damouze/SZC-1/doc/memory_chip_pinouts.xlsx

AS6C4008-55PCN |  | SST39SF040 |  |  | AS6C4008-55PCN |  |  | SST39SF040
 |  |  |  |  | BUS | UNIT | BUS | UNIT | BUS
D3 | 17 | D3 | 17 | * | A14 | 3 | A14 | 29 | A14 | 1
D4 | 18 | D4 | 18 | * | A15 | 31 | A15 | 3 | A15 | 1
A15 | 31 | /WE | 31 | * | /WE | 29 | /WE | 31 | /WE | 1
