damouze/SZC-1/boards/core/power_board_v2/production/ATX_20-PIN.png

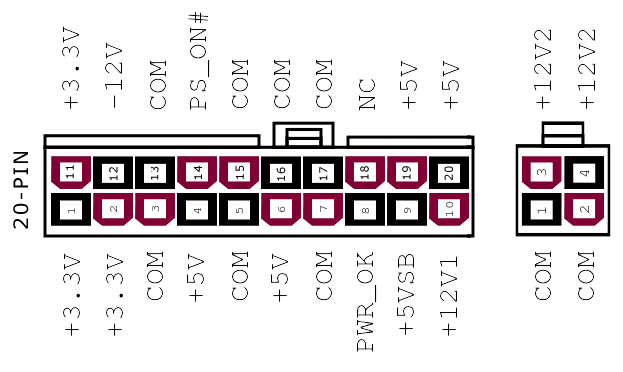
boards/core/power_board_v2/production/ATX_20-PIN.png
