damouze/SZC-1/boards/core/power_board_v2/production/J5.png

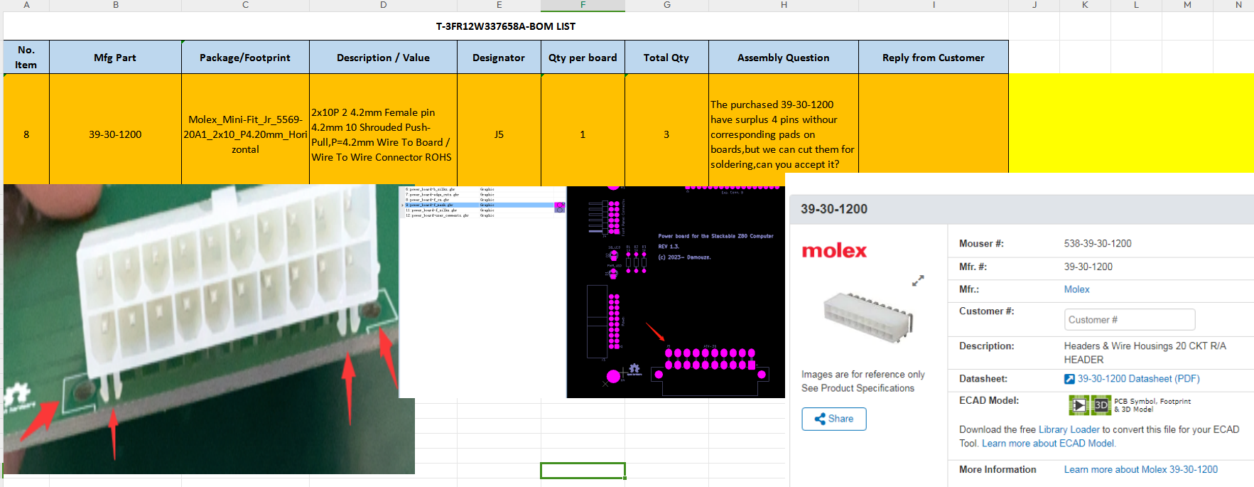
boards/core/power_board_v2/production/J5.png
