damouze/SZC-1/doc/Capture.PNG

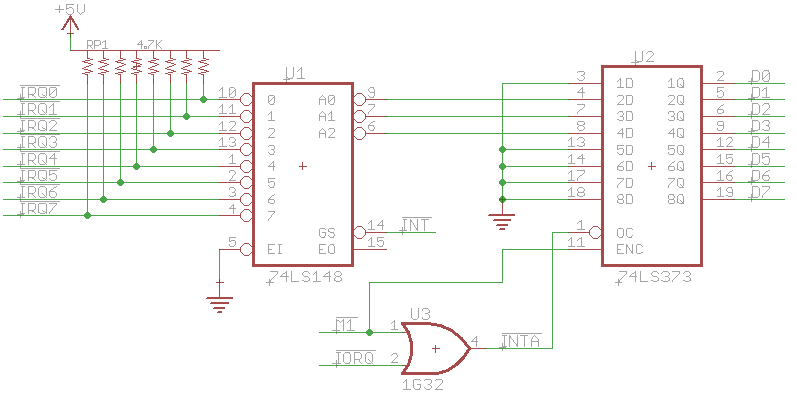
doc/Capture.PNG
