damouze/SZC-1/doc/Interrupt+Mode+2+Circuit.png

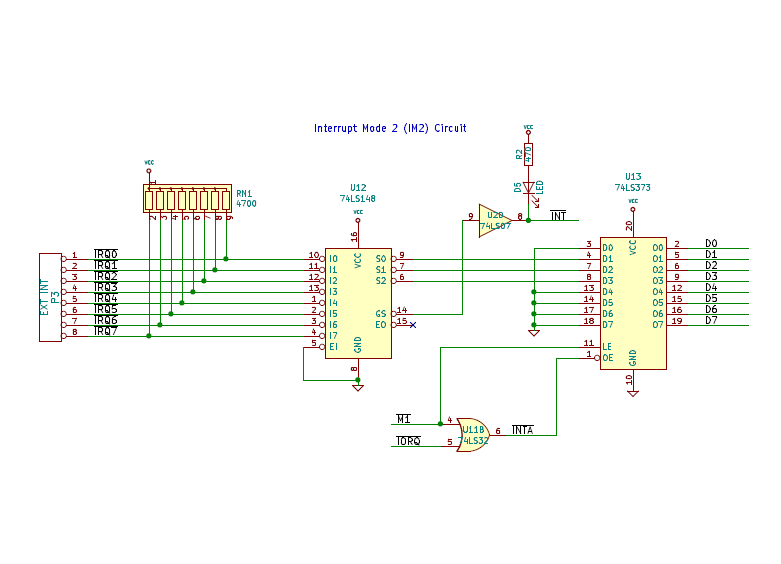
doc/Interrupt+Mode+2+Circuit.png
