damouze/SZC-1/pics/renderings/7seg_led_display_bottom.png

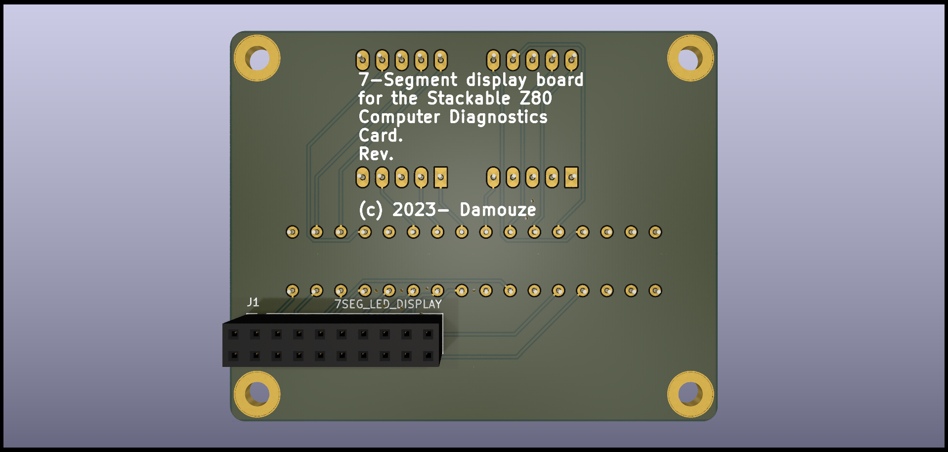
pics/renderings/7seg_led_display_bottom.png
