damouze/SZC-1/pics/renderings/7seg_led_display_top.png

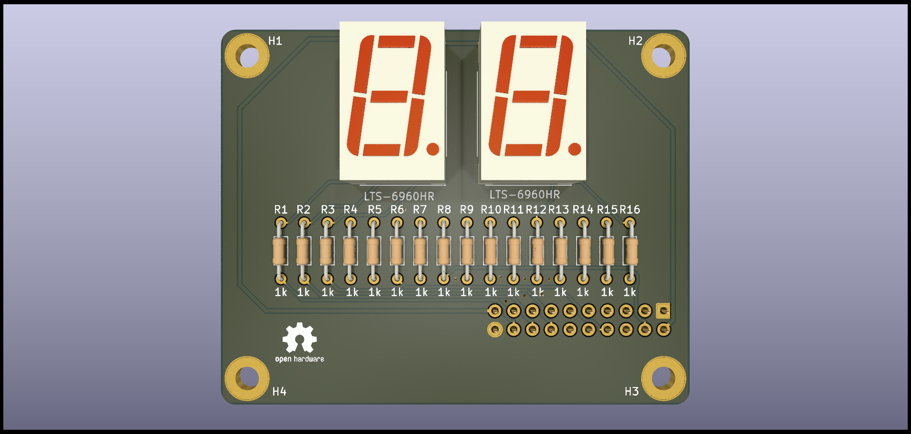
pics/renderings/7seg_led_display_top.png
