damouze/SZC-1/pics/renderings/audio_board_back.png

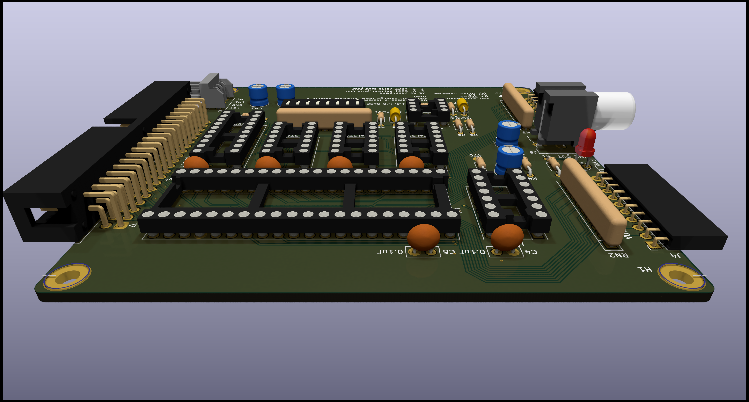
pics/renderings/audio_board_back.png
