damouze/SZC-1/pics/renderings/audio_board_bottom.png

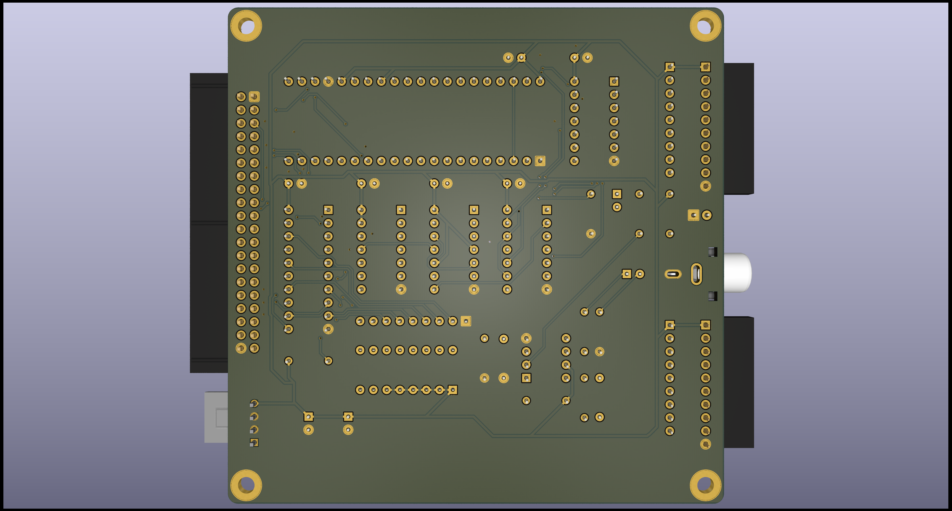
pics/renderings/audio_board_bottom.png
