damouze/SZC-1/pics/renderings/audio_board_front.png

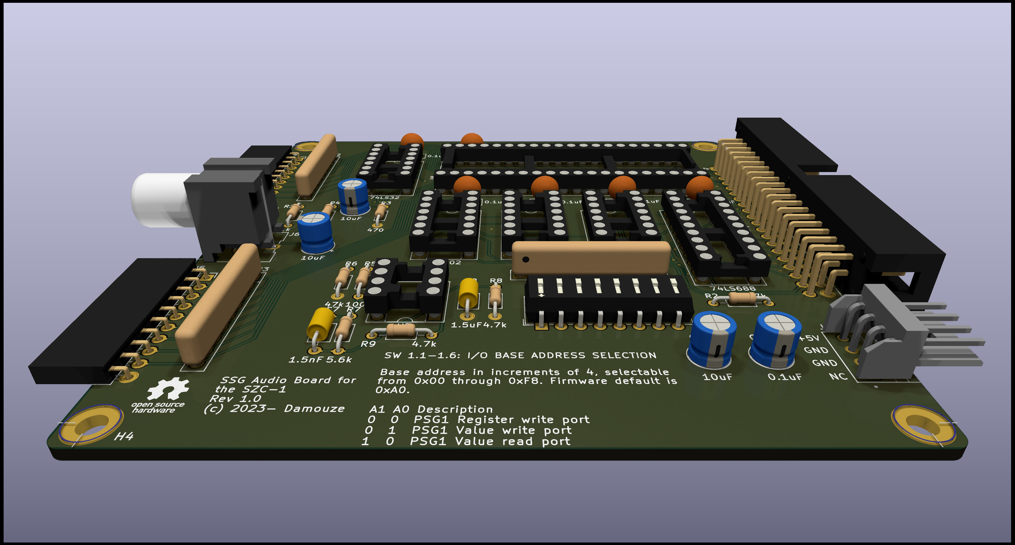
pics/renderings/audio_board_front.png
