damouze/SZC-1/pics/renderings/audio_board_left.png

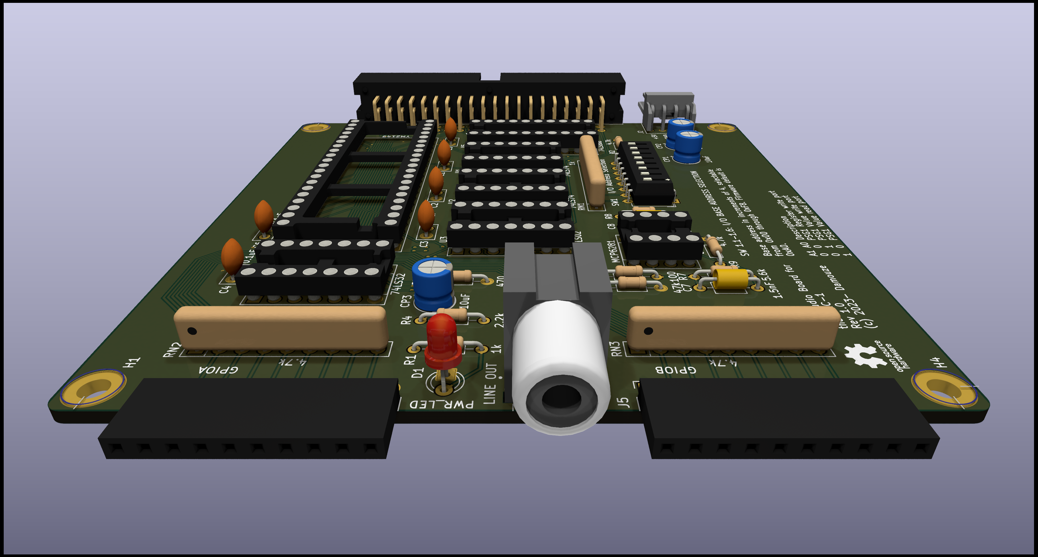
pics/renderings/audio_board_left.png
