damouze/SZC-1/pics/renderings/audio_board_left_unrouted.png

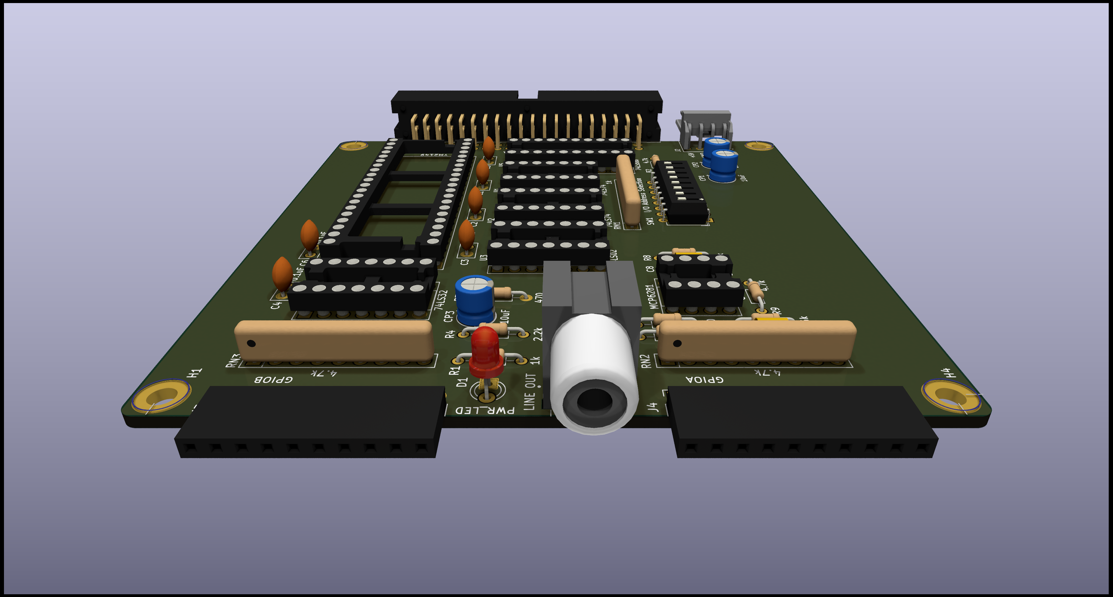
pics/renderings/audio_board_left_unrouted.png
