damouze/SZC-1/pics/renderings/audio_board_right.png

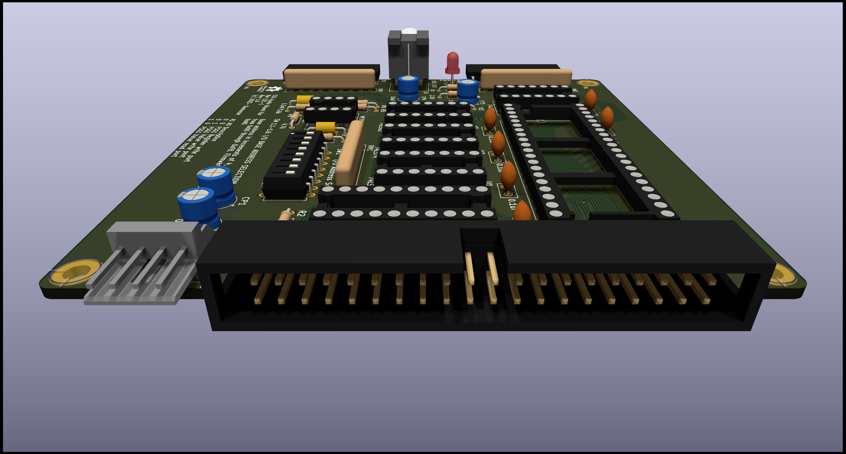
pics/renderings/audio_board_right.png
