damouze/SZC-1/pics/renderings/audio_board_top.png

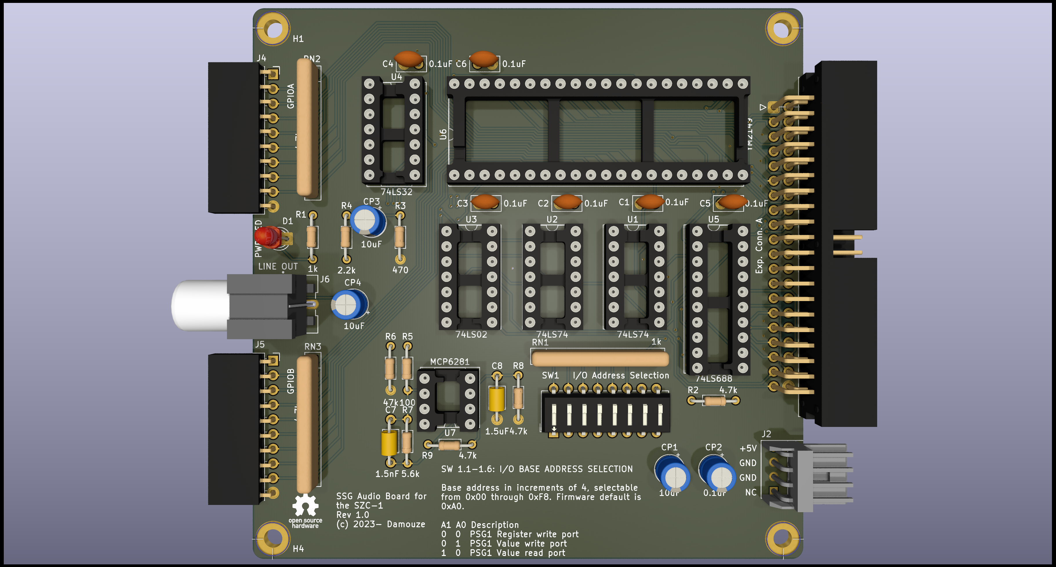
pics/renderings/audio_board_top.png
