damouze/SZC-1/pics/renderings/bus_decode.png

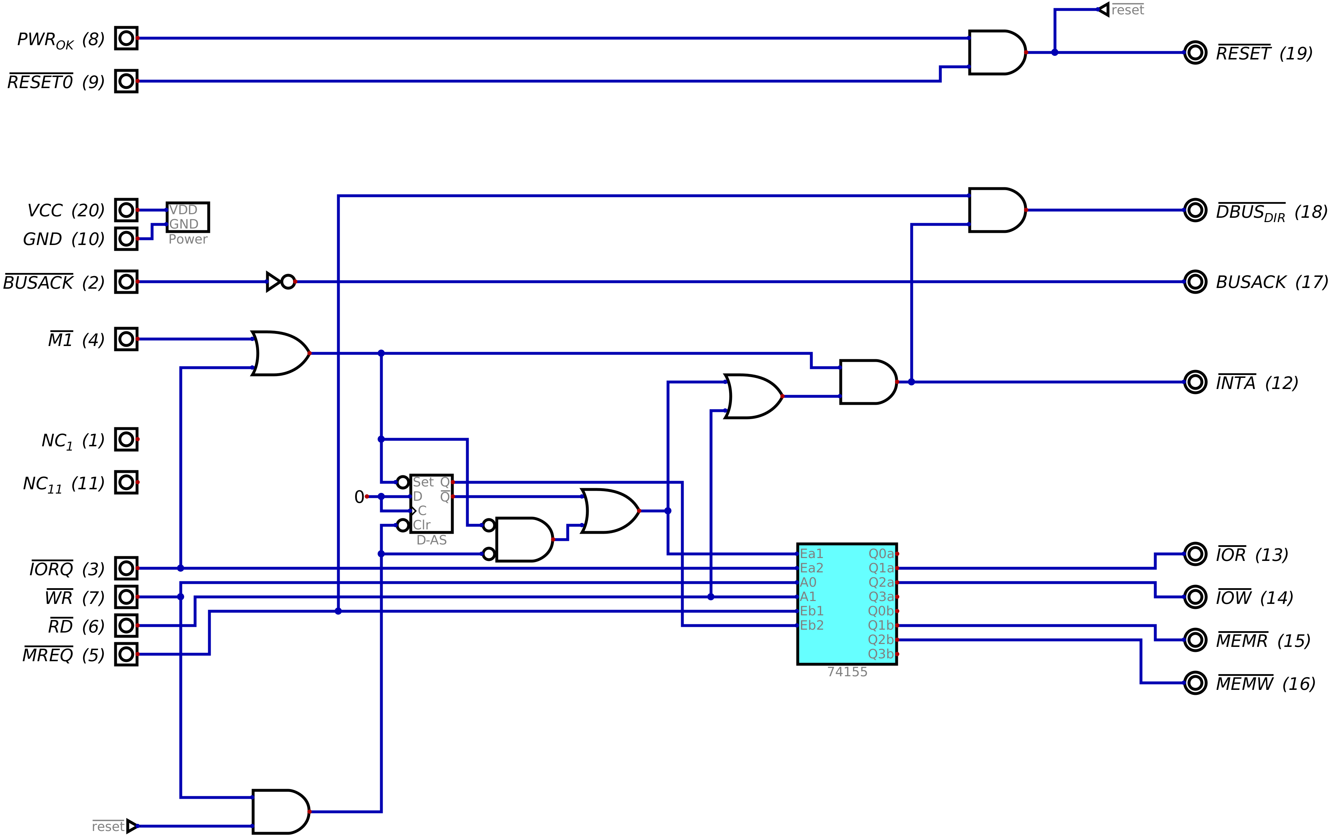
pics/renderings/bus_decode.png
