damouze/SZC-1/pics/renderings/clock_reset_board_top.png

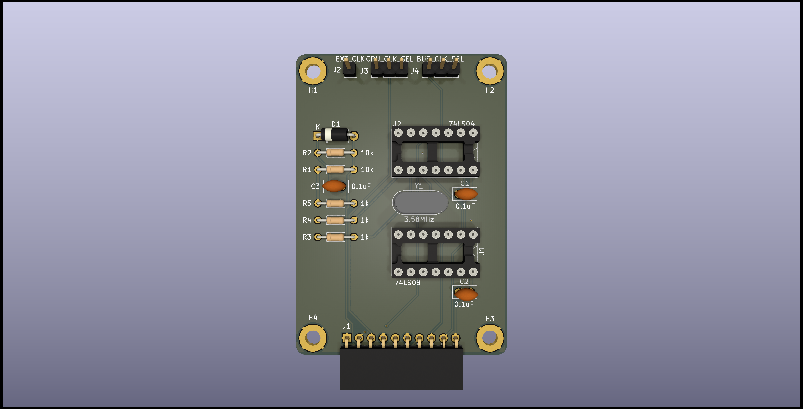
pics/renderings/clock_reset_board_top.png
