damouze/SZC-1/pics/renderings/cpu_board_ext_bus_bottom.png

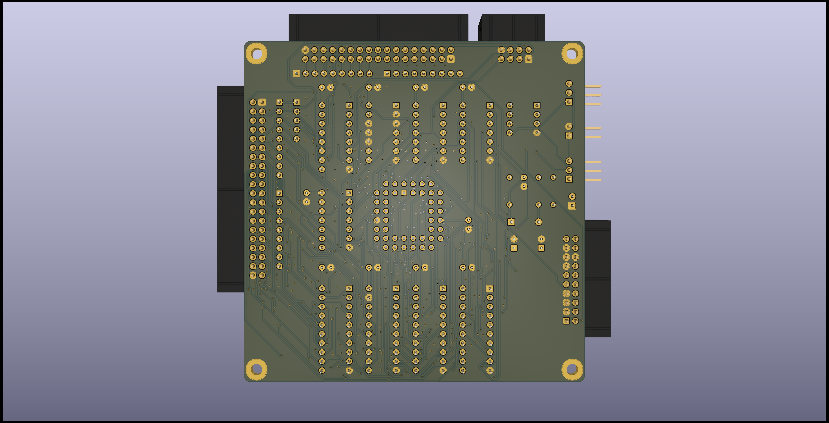
pics/renderings/cpu_board_ext_bus_bottom.png
