damouze/SZC-1/pics/renderings/cpu_board_ext_bus_top.png

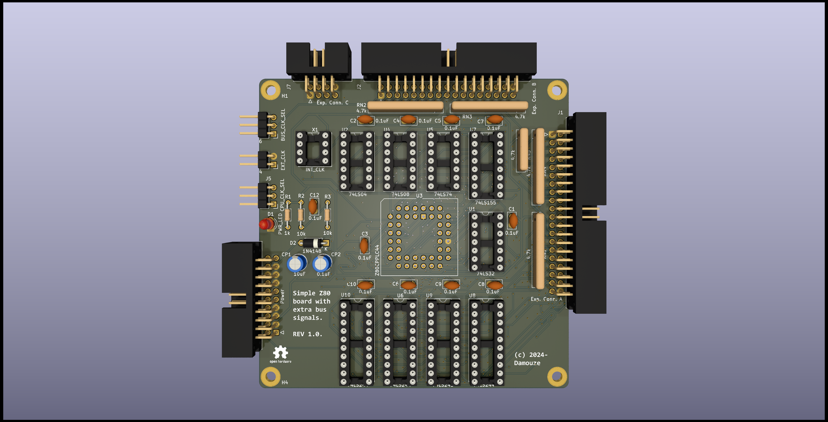
pics/renderings/cpu_board_ext_bus_top.png
