damouze/SZC-1/pics/renderings/cpu_board_ext_bus_v2_back.png

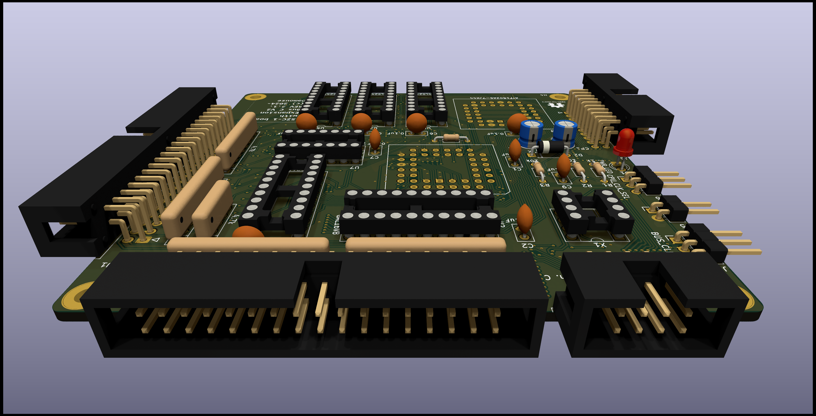
pics/renderings/cpu_board_ext_bus_v2_back.png
