damouze/SZC-1/pics/renderings/cpu_board_ext_bus_v2_left.png

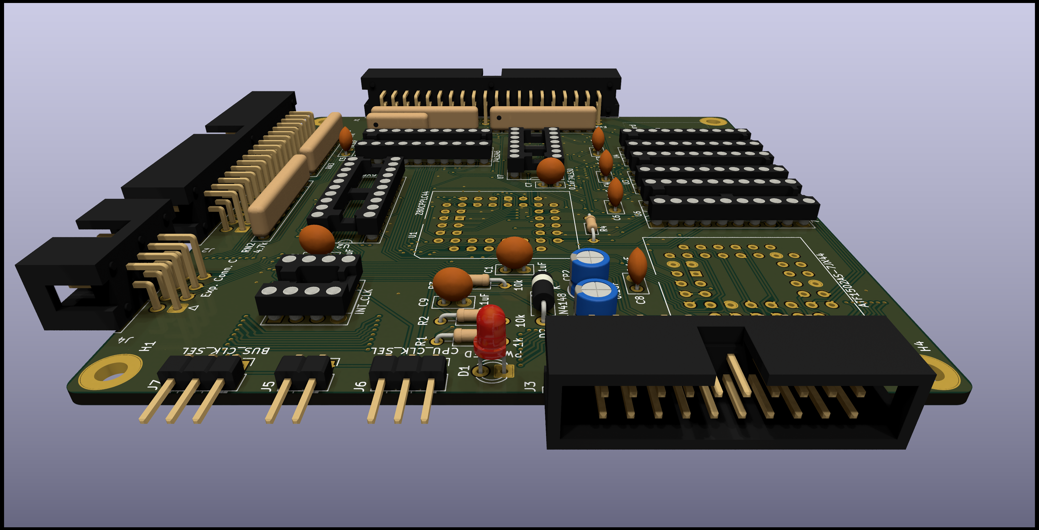
pics/renderings/cpu_board_ext_bus_v2_left.png
