damouze/SZC-1/pics/renderings/diag_board_bottom.png

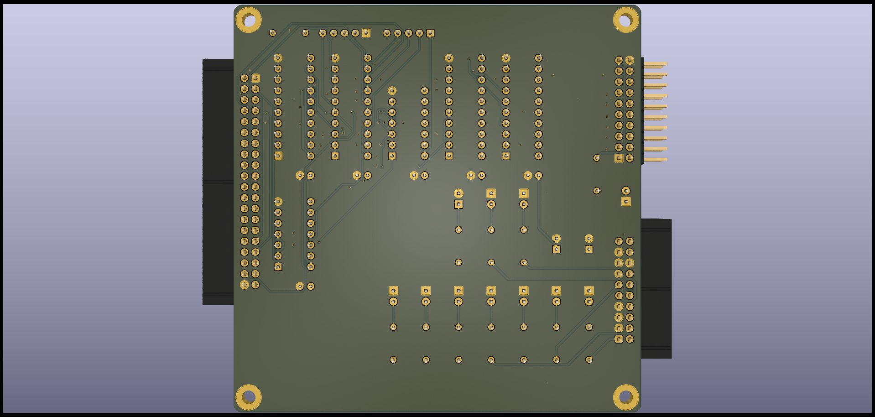
pics/renderings/diag_board_bottom.png
