damouze/SZC-1/pics/renderings/diag_board_left.png

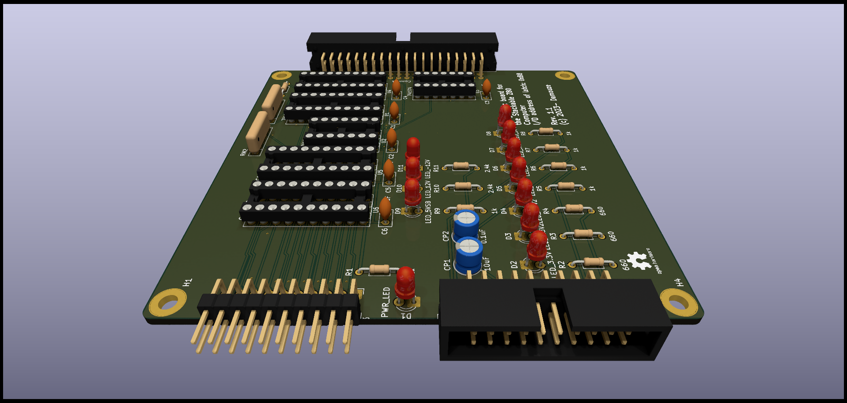
pics/renderings/diag_board_left.png
