damouze/SZC-1/pics/renderings/diag_board_top.png

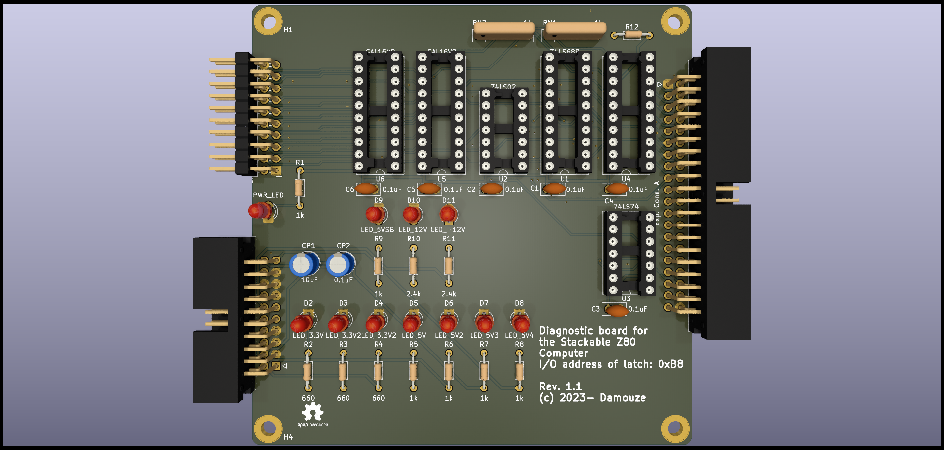
pics/renderings/diag_board_top.png
