damouze/SZC-1/pics/renderings/even_simpler_z80_bottom.png

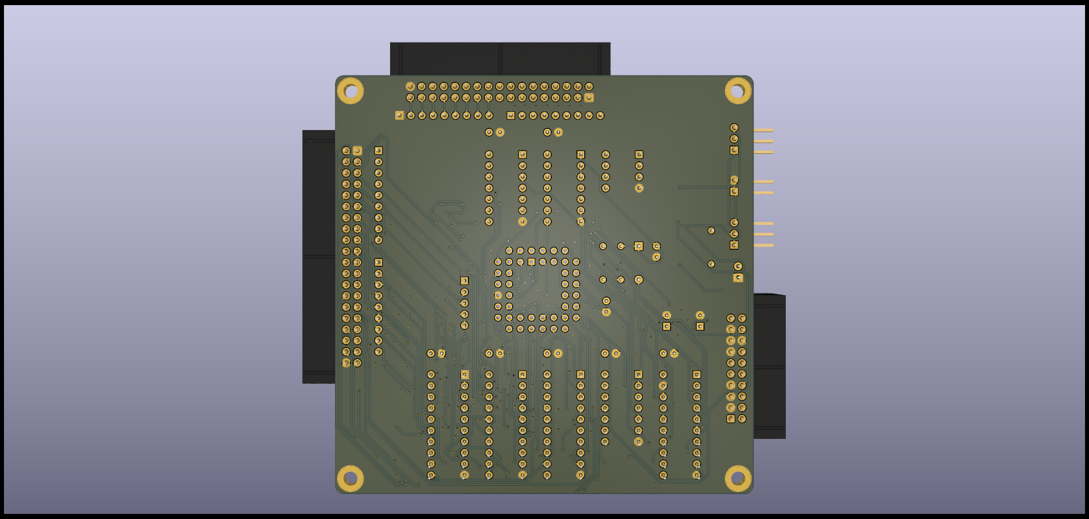
pics/renderings/even_simpler_z80_bottom.png
