damouze/SZC-1/pics/renderings/even_simpler_z80_front.png

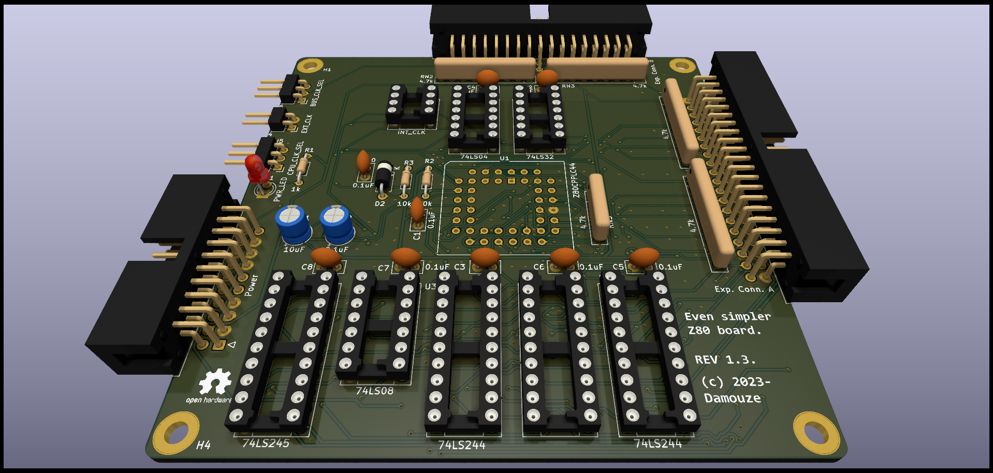
pics/renderings/even_simpler_z80_front.png
