damouze/SZC-1/pics/renderings/even_simpler_z80_top.png

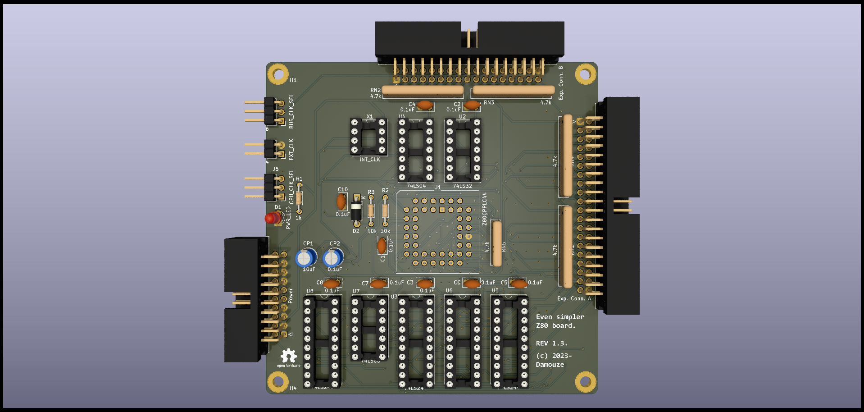
pics/renderings/even_simpler_z80_top.png
