damouze/SZC-1/pics/renderings/ide_board_top.png

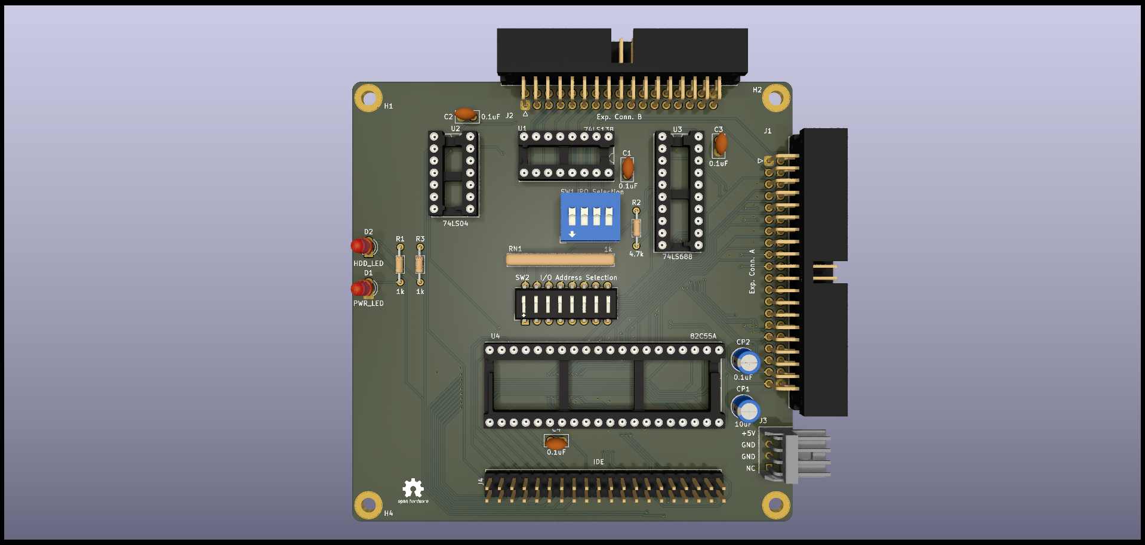
pics/renderings/ide_board_top.png
