damouze/SZC-1/pics/renderings/io_board_back.png

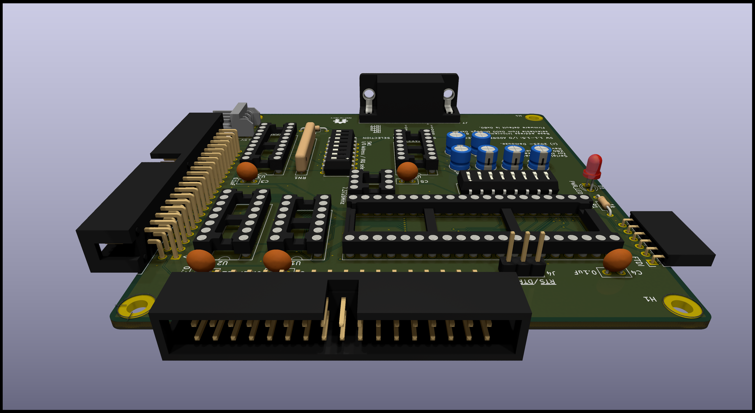
pics/renderings/io_board_back.png
