damouze/SZC-1/pics/renderings/io_board_bottom.png

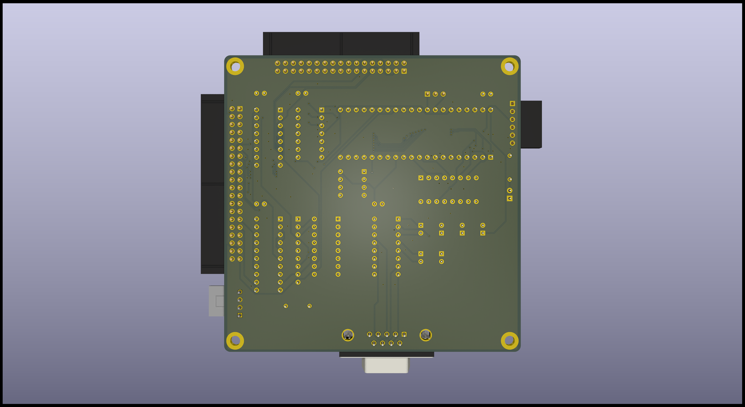
pics/renderings/io_board_bottom.png
