damouze/SZC-1/pics/renderings/io_board_front.png

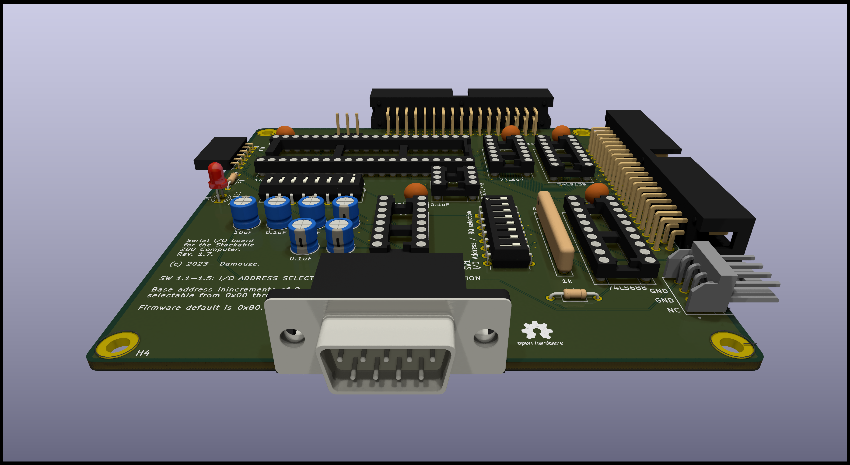
pics/renderings/io_board_front.png
