damouze/SZC-1/pics/renderings/io_board_left.png

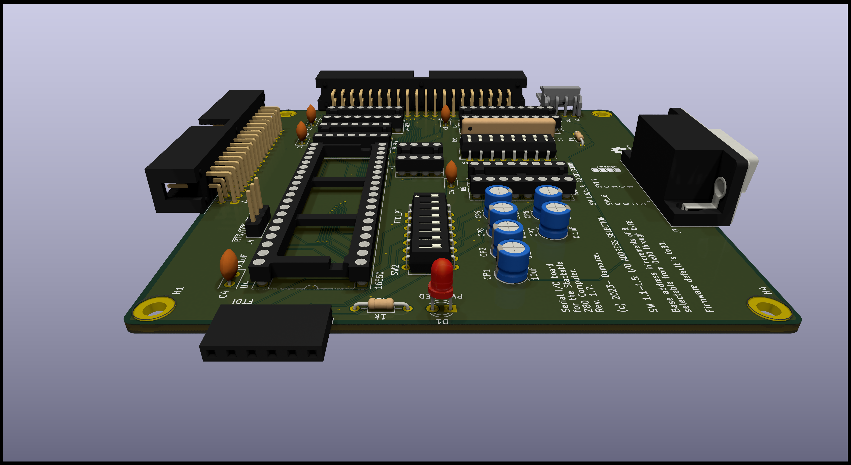
pics/renderings/io_board_left.png
