damouze/SZC-1/pics/renderings/io_board_right.png

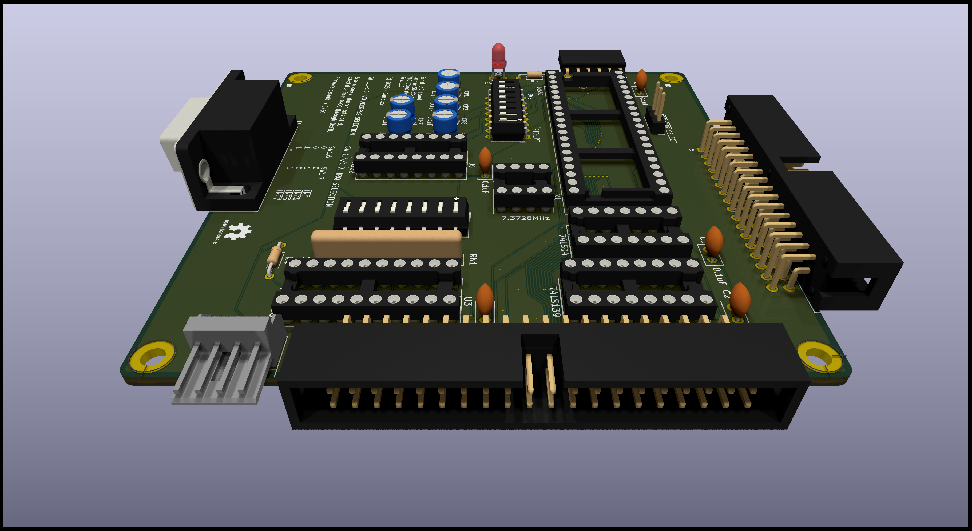
pics/renderings/io_board_right.png
