damouze/SZC-1/pics/renderings/io_board_top.png

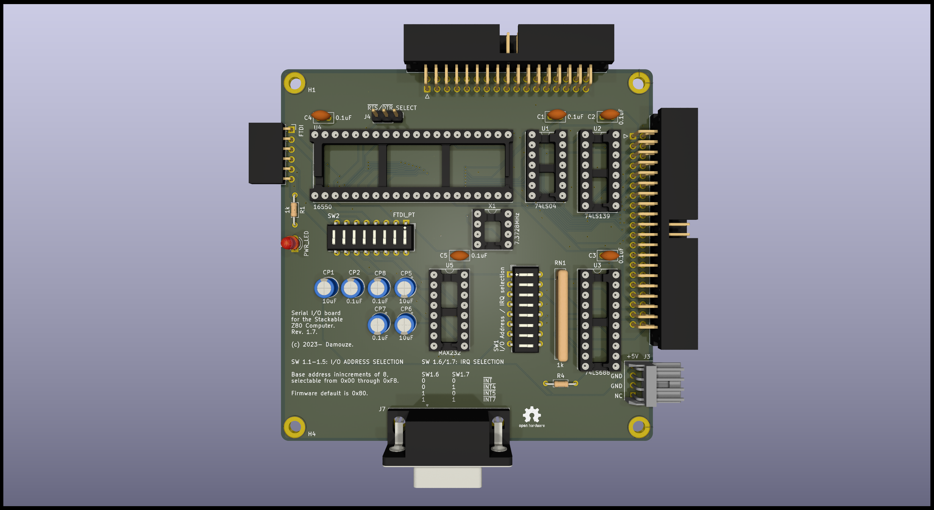
pics/renderings/io_board_top.png
