damouze/SZC-1/pics/renderings/msx_rom_ram_board_front.png

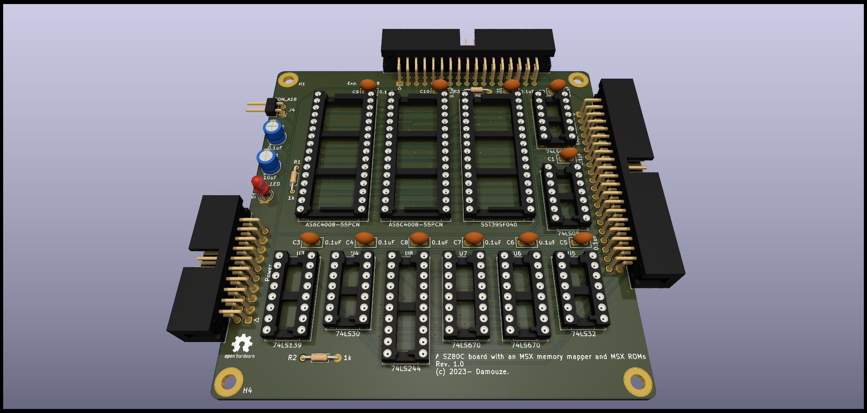
pics/renderings/msx_rom_ram_board_front.png
