damouze/SZC-1/pics/renderings/power_board_bottom.png

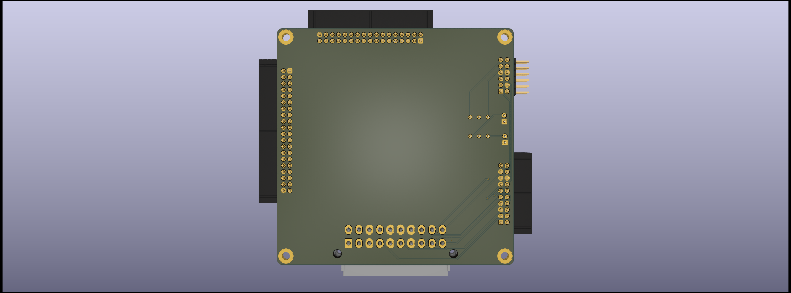
pics/renderings/power_board_bottom.png
