damouze/SZC-1/pics/renderings/power_board_left.png

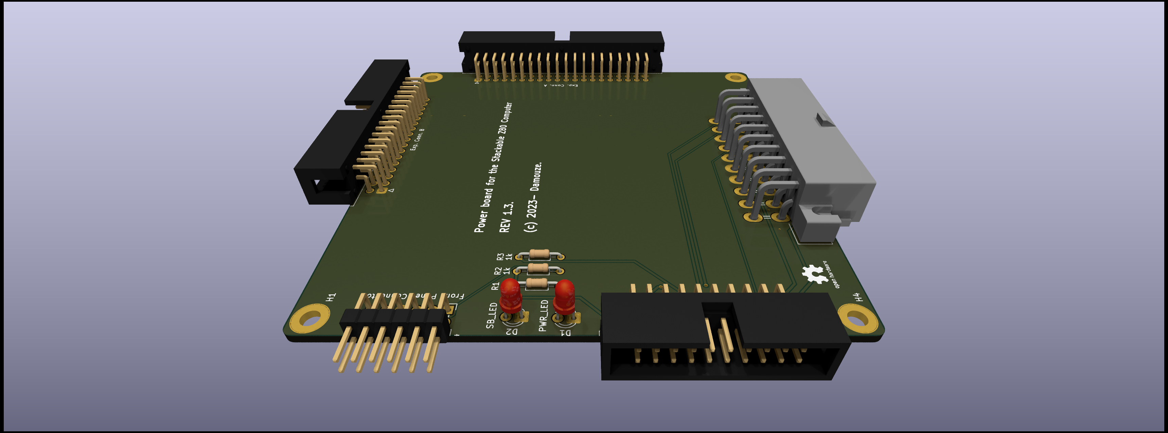
pics/renderings/power_board_left.png
