damouze/SZC-1/pics/renderings/power_board_top.png

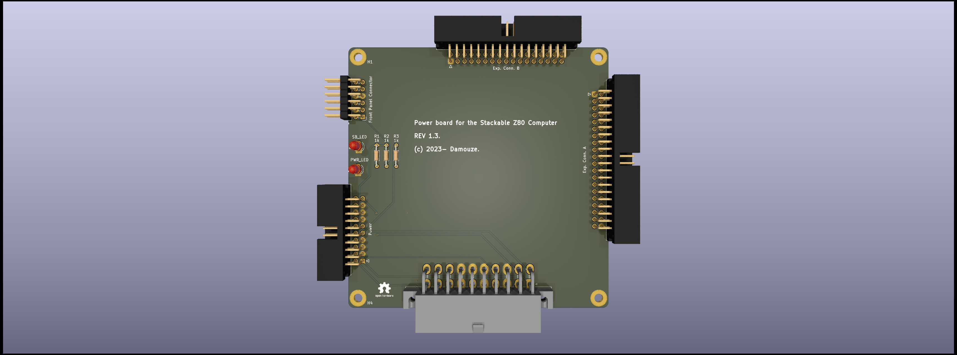
pics/renderings/power_board_top.png
