damouze/SZC-1/pics/renderings/power_board_v2_back.png

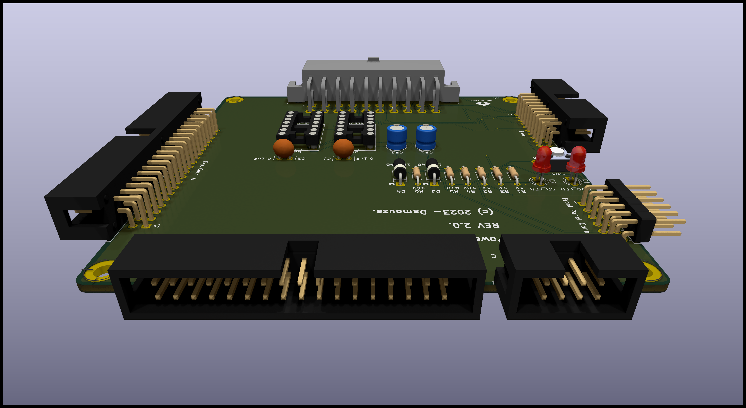
pics/renderings/power_board_v2_back.png
