damouze/SZC-1/pics/renderings/power_board_v2_front.png

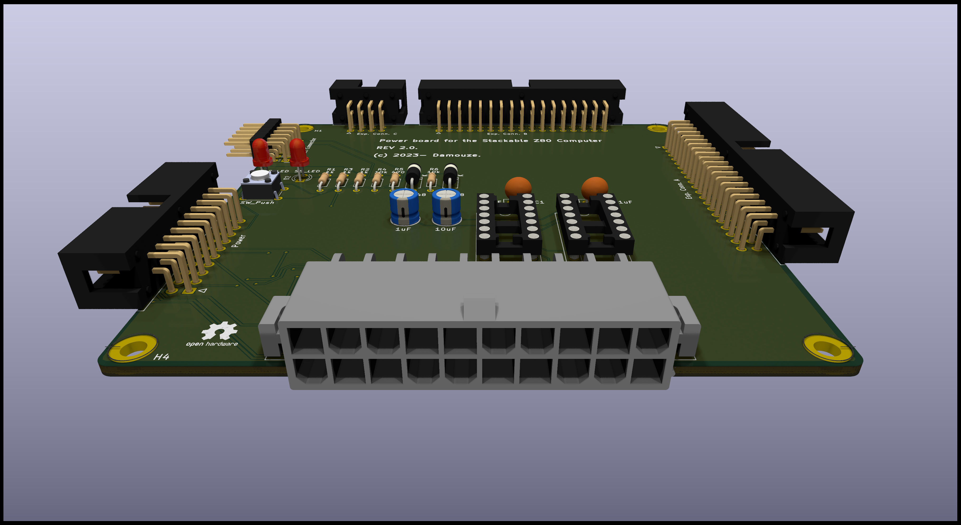
pics/renderings/power_board_v2_front.png
