damouze/SZC-1/pics/renderings/power_board_v2_left.png

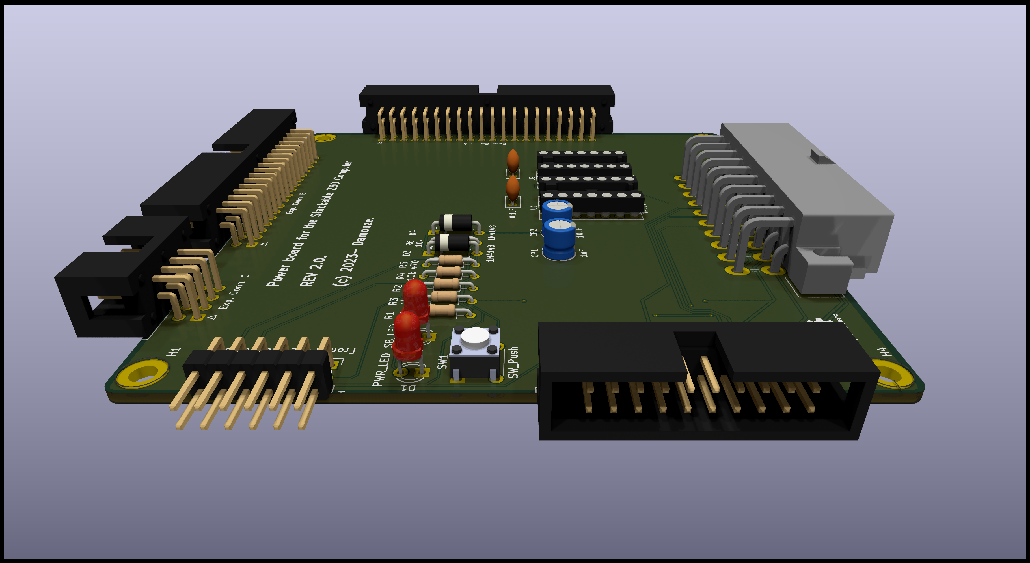
pics/renderings/power_board_v2_left.png
