damouze/SZC-1/pics/renderings/power_board_v2_right.png

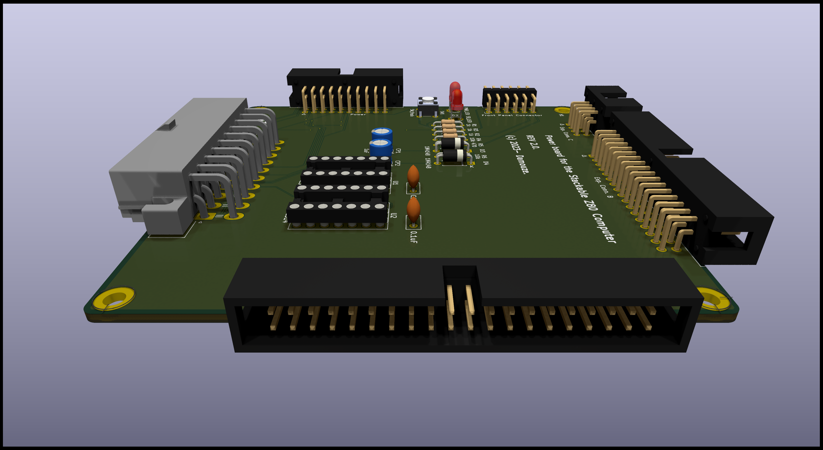
pics/renderings/power_board_v2_right.png
