damouze/SZC-1/pics/renderings/power_board_v2_top.png

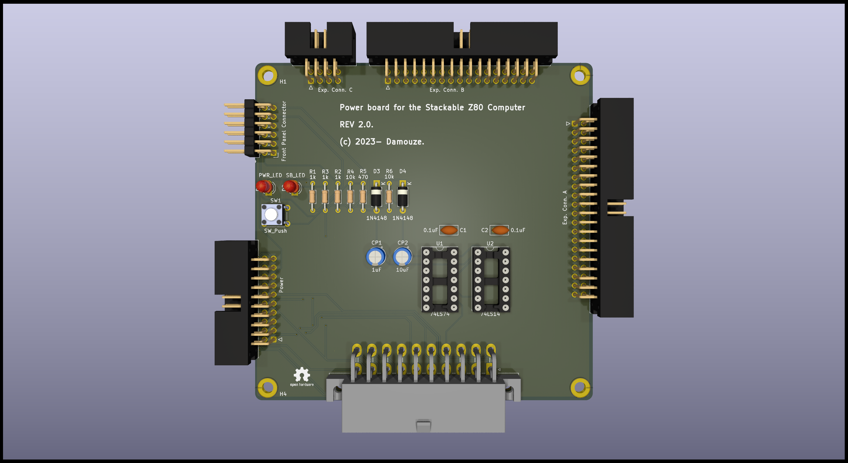
pics/renderings/power_board_v2_top.png
