damouze/SZC-1/pics/renderings/ppi_slot_select_expanded_front.png

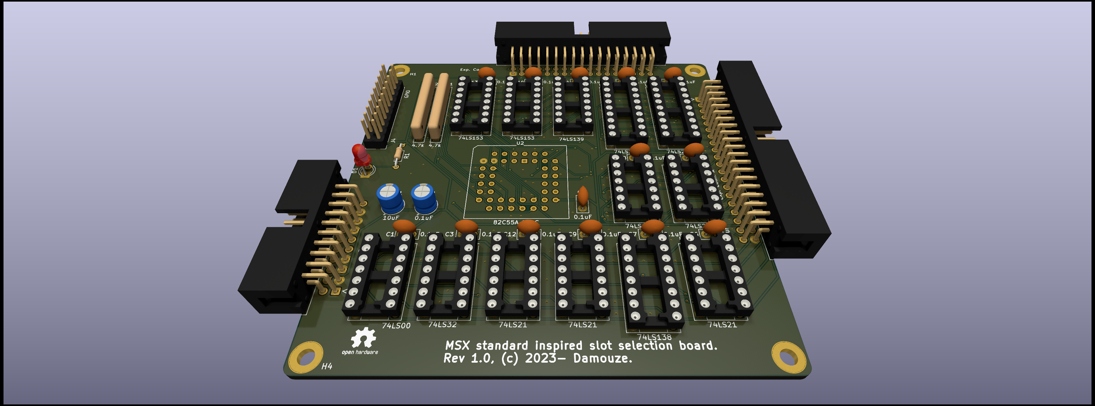
pics/renderings/ppi_slot_select_expanded_front.png
