damouze/SZC-1/pics/renderings/ppi_slot_select_expanded_top.png

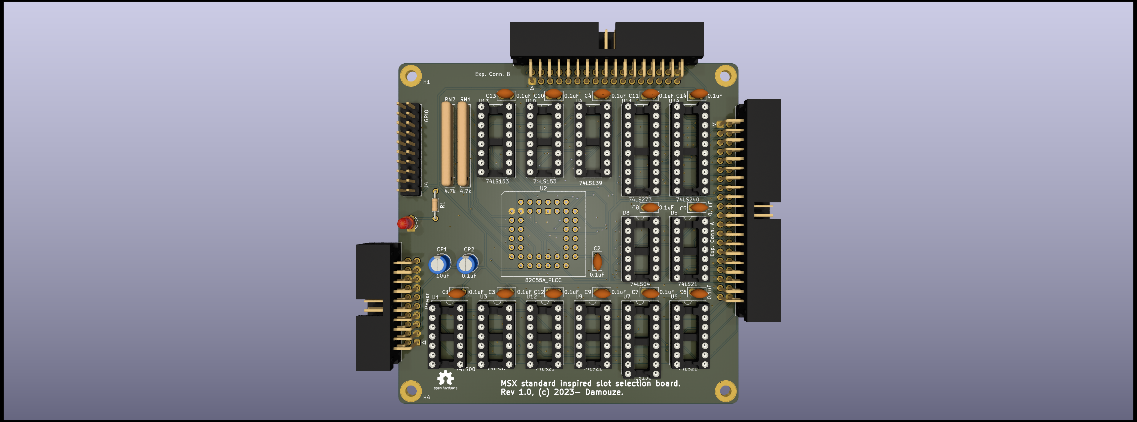
pics/renderings/ppi_slot_select_expanded_top.png
