damouze/SZC-1/pics/renderings/ppi_slot_select_left.png

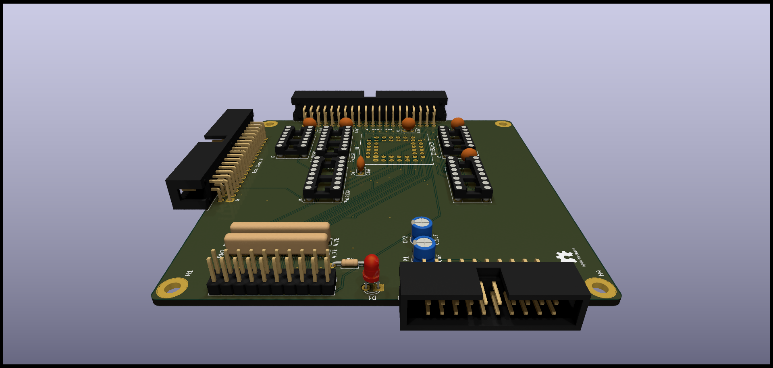
pics/renderings/ppi_slot_select_left.png
