damouze/SZC-1/pics/renderings/ppi_slot_select_top.png

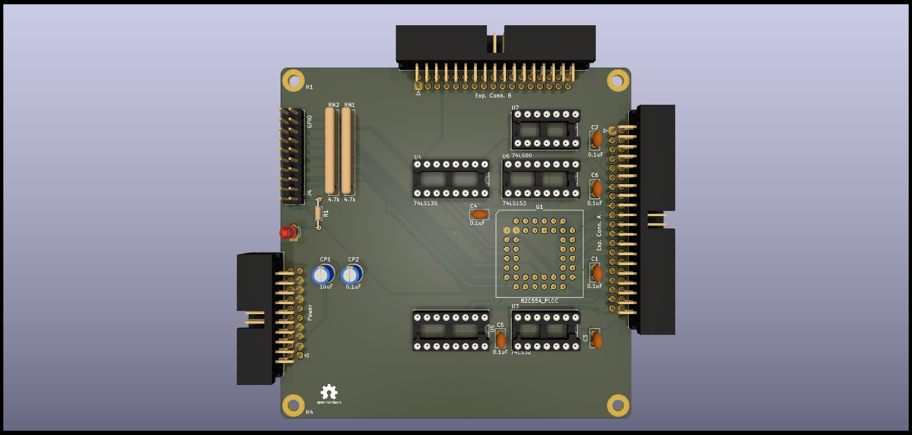
pics/renderings/ppi_slot_select_top.png
