damouze/SZC-1/pics/renderings/rom_board_512kB_v2_back.png

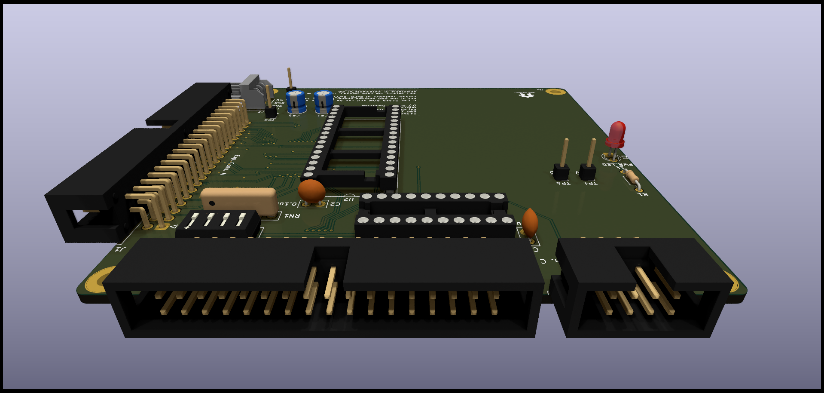
pics/renderings/rom_board_512kB_v2_back.png
