damouze/SZC-1/pics/renderings/rom_board_512kB_v2_front.png

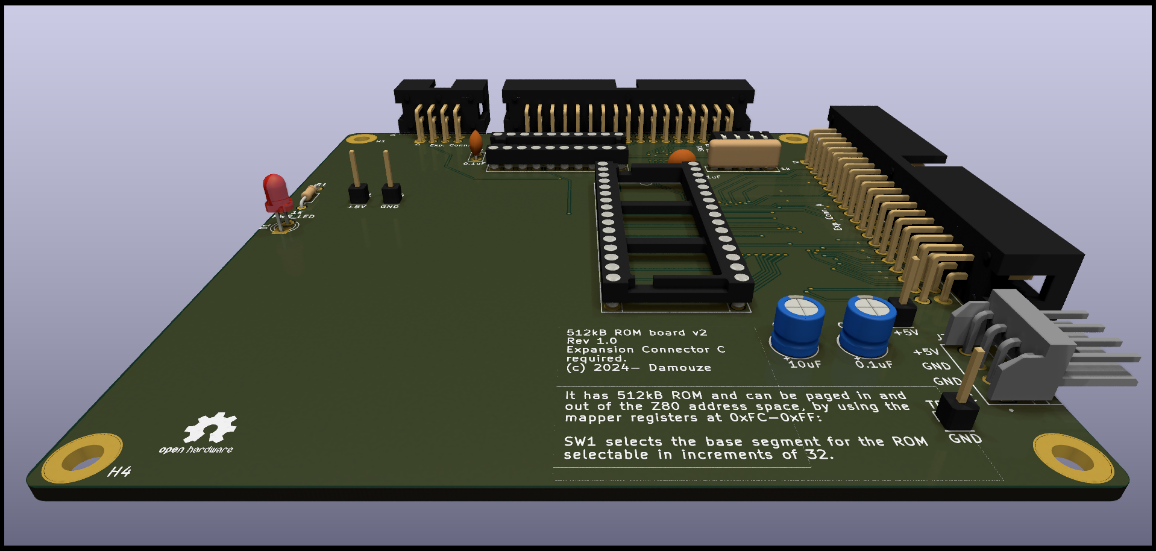
pics/renderings/rom_board_512kB_v2_front.png
