damouze/SZC-1/pics/renderings/rom_board_512kB_v2_left.png

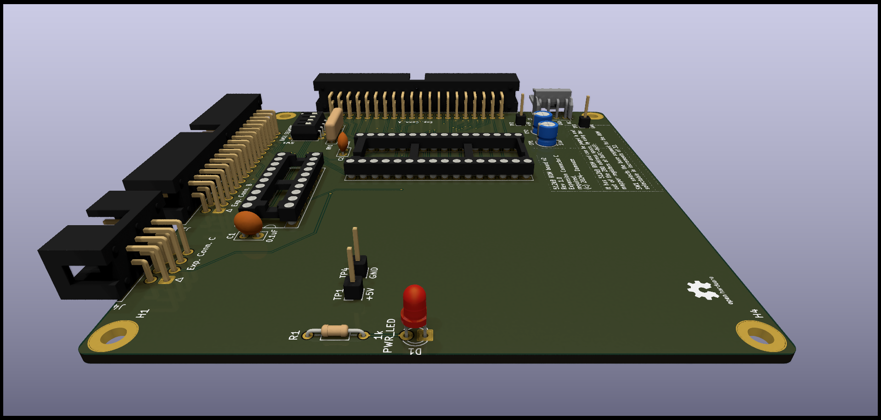
pics/renderings/rom_board_512kB_v2_left.png
