damouze/SZC-1/pics/renderings/rom_ram_board_2MB_front.png

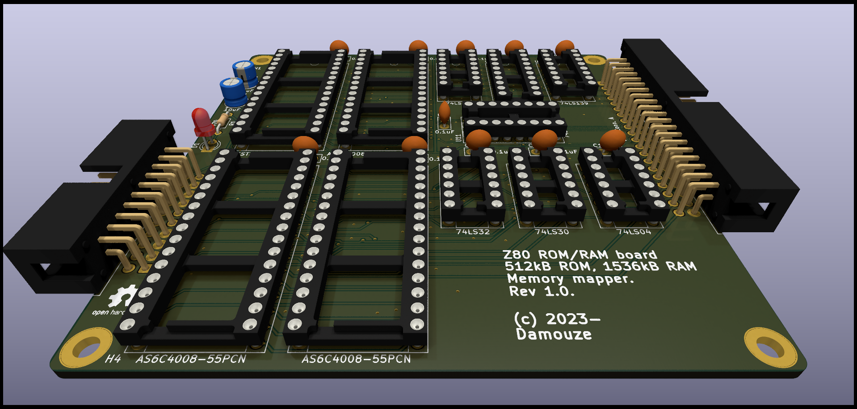
pics/renderings/rom_ram_board_2MB_front.png
