damouze/SZC-1/pics/renderings/rom_ram_board_128kB_v2_top.png

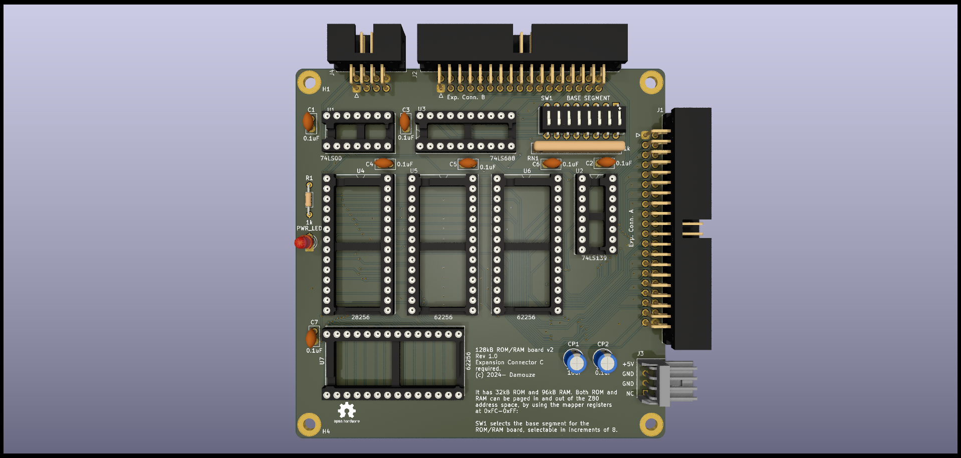
pics/renderings/rom_ram_board_128kB_v2_top.png
