damouze/SZC-1/pics/renderings/rom_ram_board_bottom.png

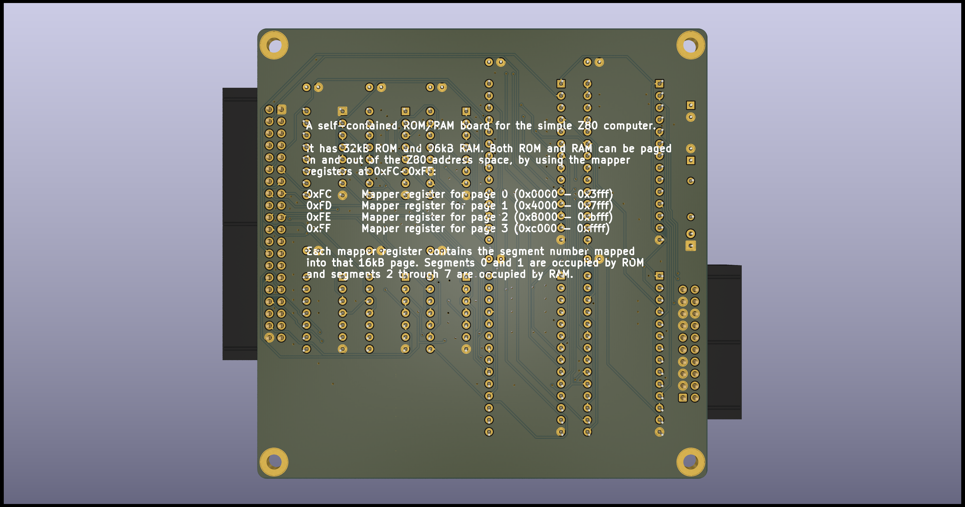
pics/renderings/rom_ram_board_bottom.png
