damouze/SZC-1/pics/renderings/rom_ram_board_front.png

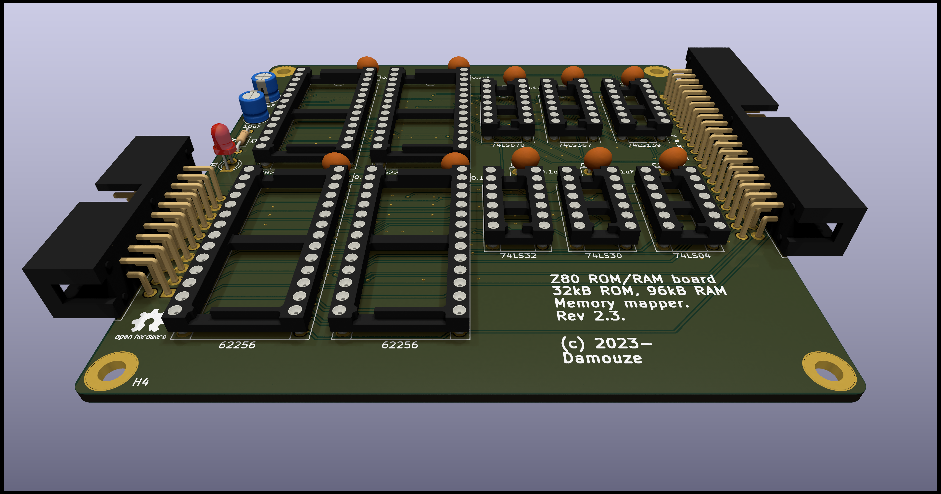
pics/renderings/rom_ram_board_front.png
