damouze/SZC-1/pics/renderings/rom_ram_board_v2_back.png

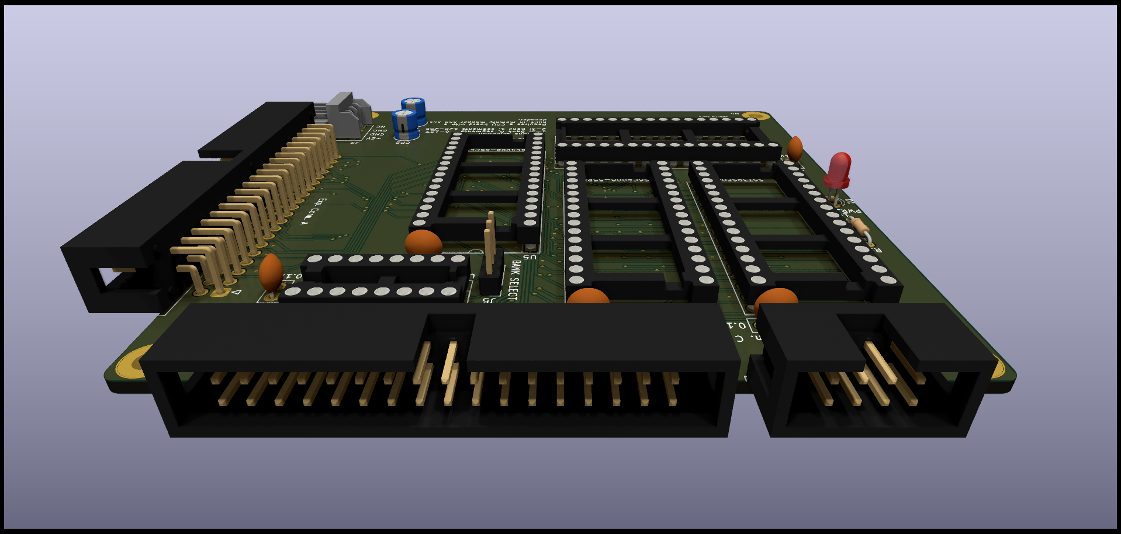
pics/renderings/rom_ram_board_v2_back.png
