damouze/SZC-1/pics/renderings/rom_ram_board_v3_back.png

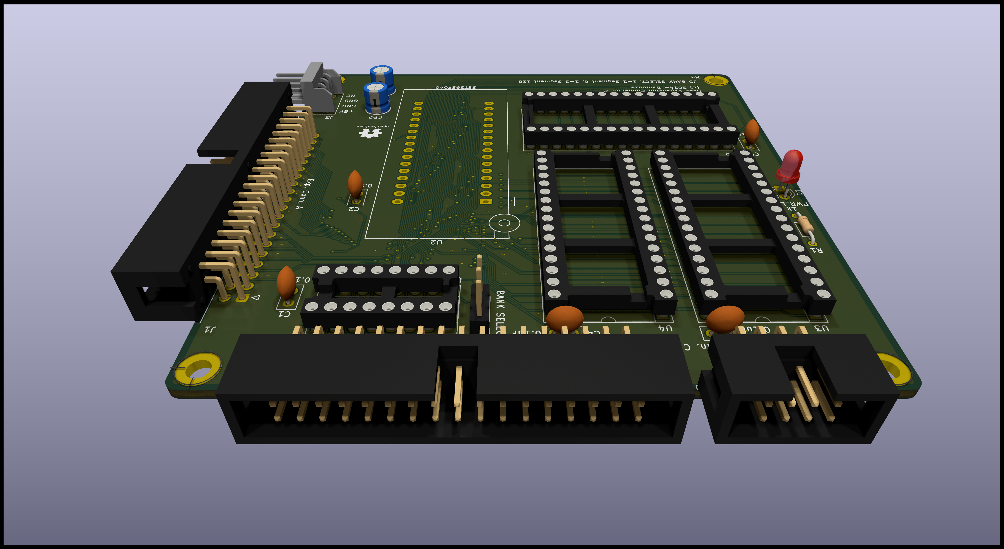
pics/renderings/rom_ram_board_v3_back.png
