damouze/SZC-1/pics/renderings/rom_ram_board_v3_left.png

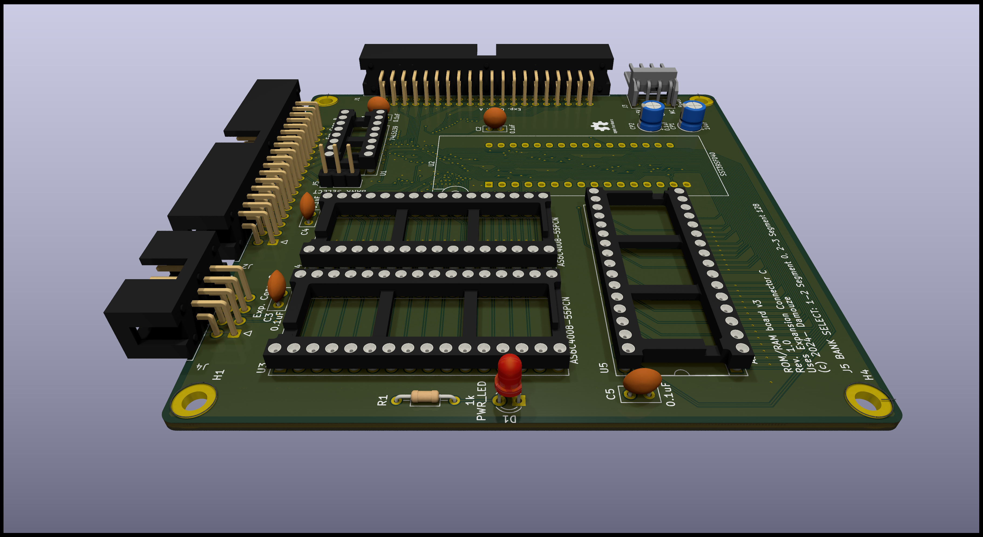
pics/renderings/rom_ram_board_v3_left.png
