damouze/SZC-1/pics/renderings/rtc_timer_board_back.png

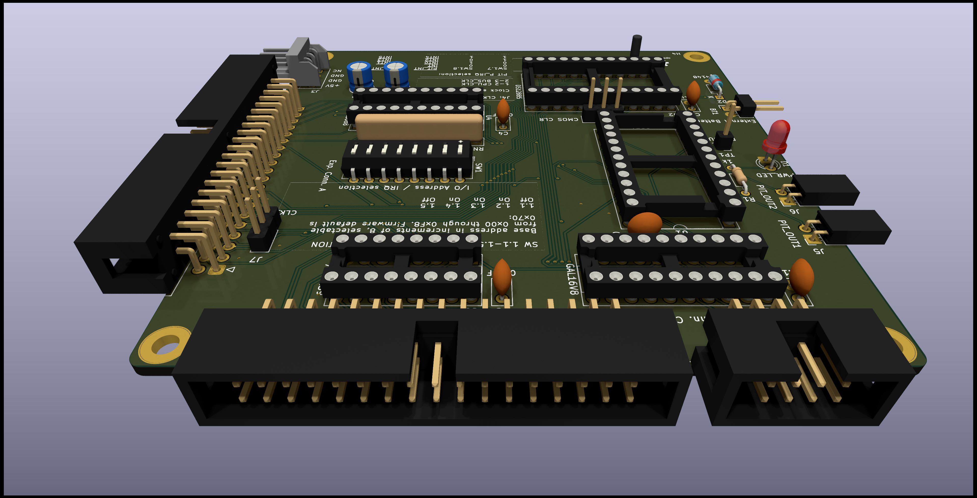
pics/renderings/rtc_timer_board_back.png
