damouze/SZC-1/pics/renderings/rtc_timer_board_left.png

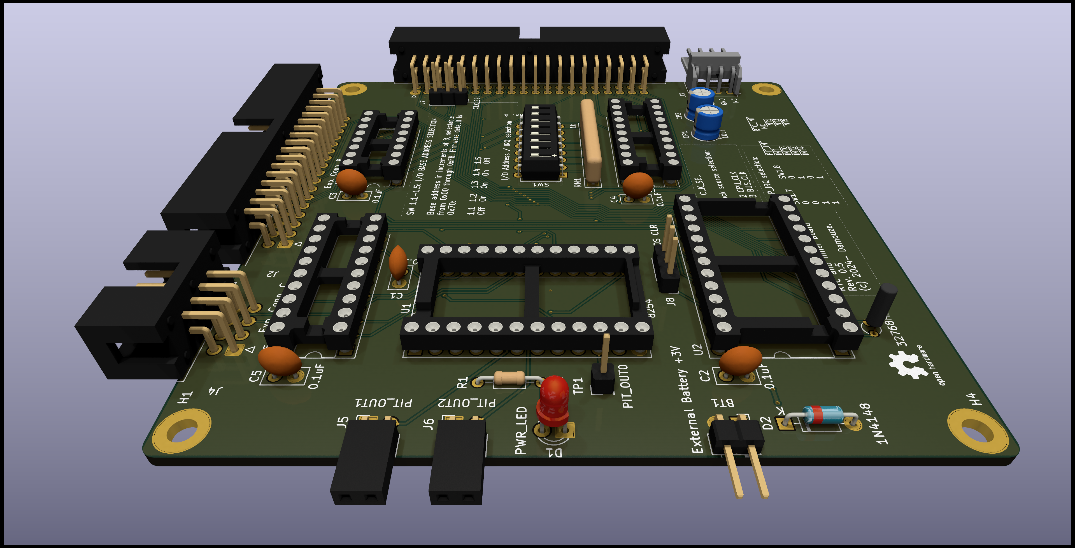
pics/renderings/rtc_timer_board_left.png
