damouze/SZC-1/pics/renderings/rtc_timer_board_right.png

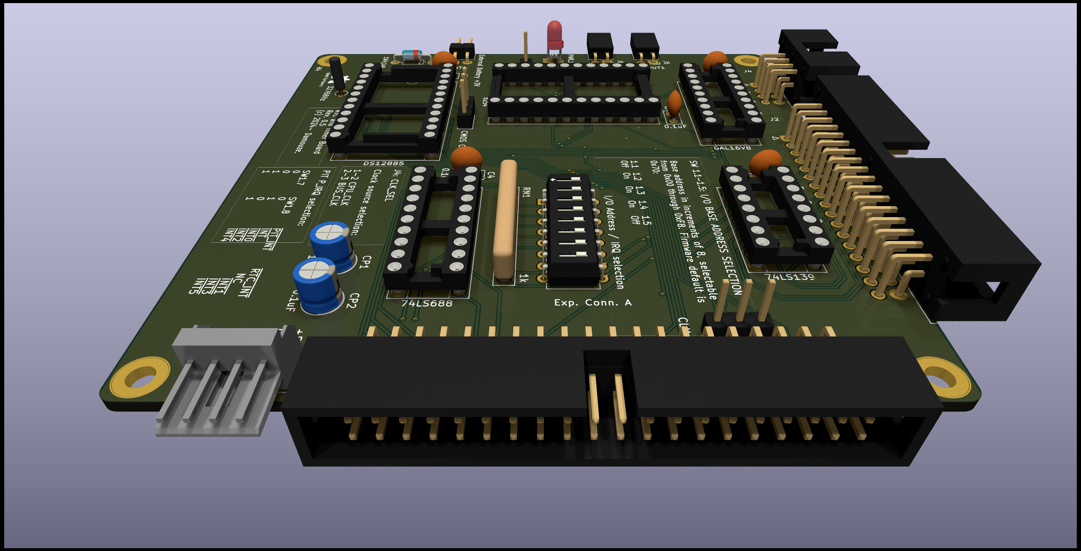
pics/renderings/rtc_timer_board_right.png
