damouze/SZC-1/pics/renderings/serial_io_board_back.png

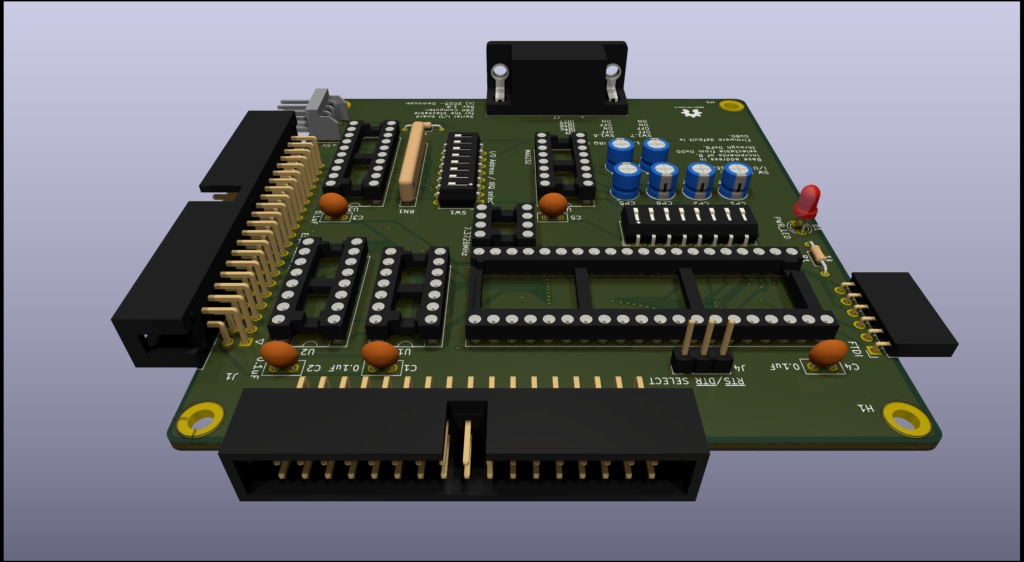
pics/renderings/serial_io_board_back.png
