damouze/SZC-1/pics/renderings/serial_io_board_bottom.png

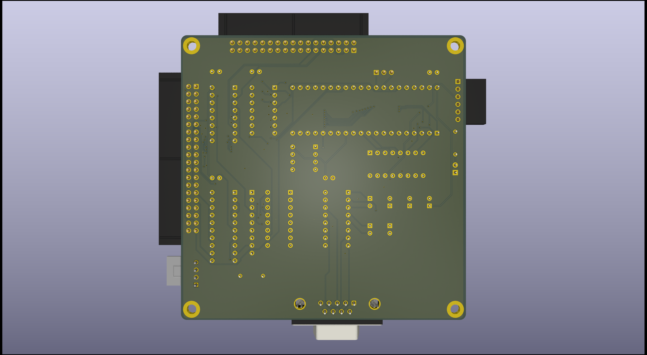
pics/renderings/serial_io_board_bottom.png
