damouze/SZC-1/pics/renderings/serial_io_board_front.png

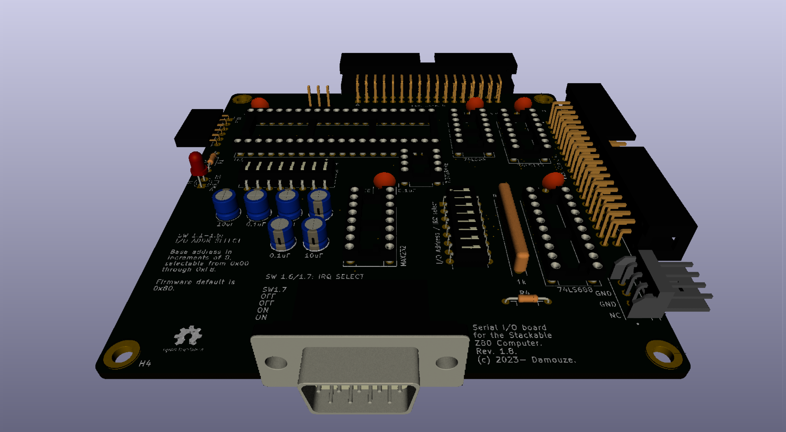
pics/renderings/serial_io_board_front.png
