damouze/SZC-1/pics/renderings/serial_io_board_left.png

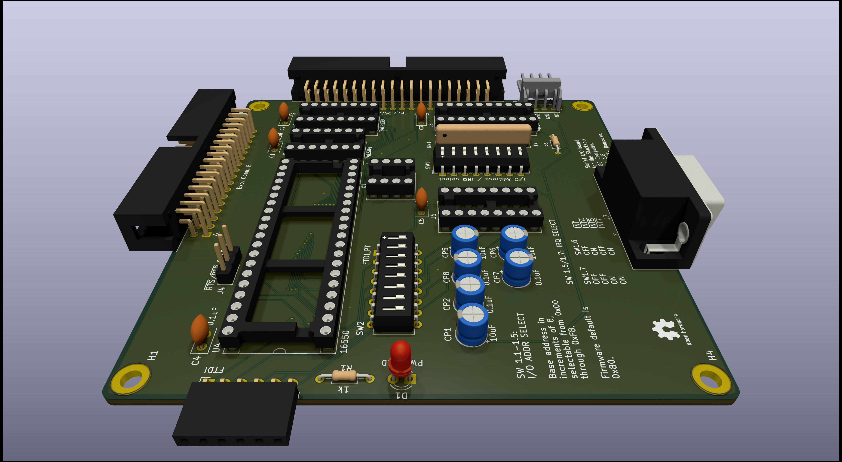
pics/renderings/serial_io_board_left.png
