damouze/SZC-1/pics/renderings/serial_io_board_right.png

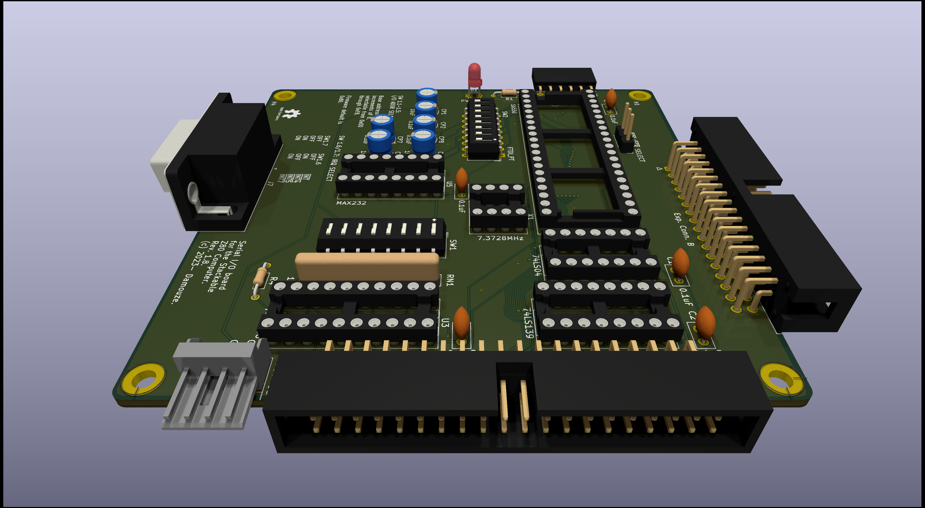
pics/renderings/serial_io_board_right.png
