damouze/SZC-1/pics/renderings/simple_z80_front.png

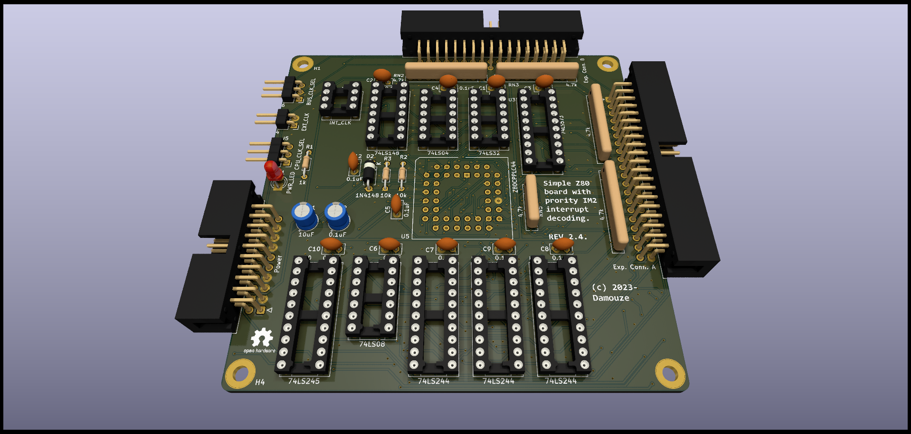
pics/renderings/simple_z80_front.png
