damouze/SZC-1/pics/renderings/simple_z80_top.png

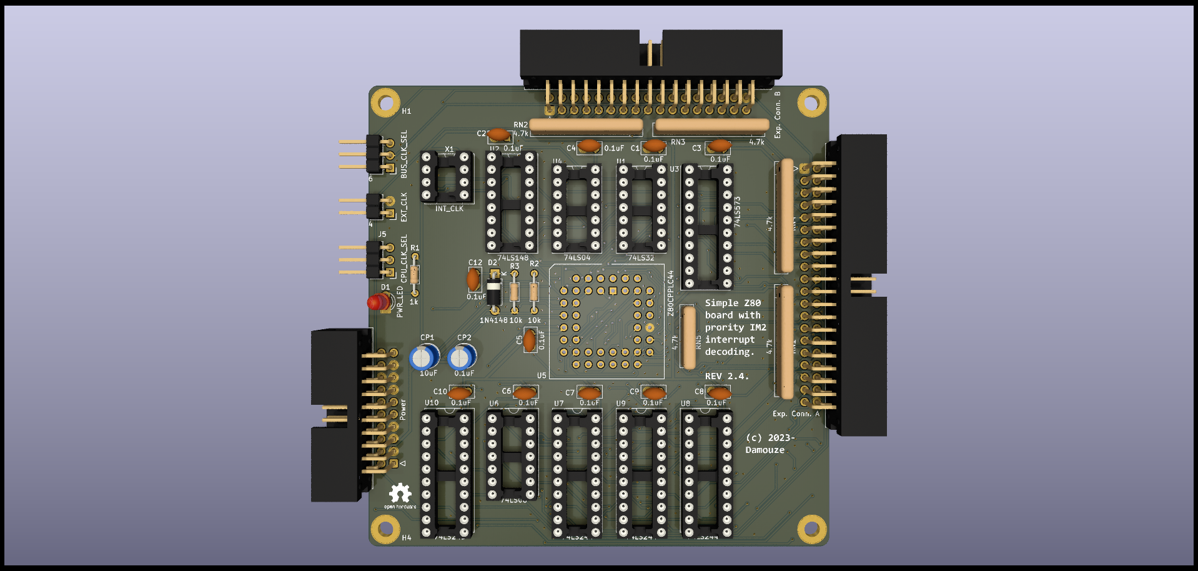
pics/renderings/simple_z80_top.png
