damouze/SZC-1/digital/im2_int_ctrlr/test.csv

step | ~{INTA} | ~{CPU_INT} | UP | DOWN | LEFT | RIGHT | 4 | 5 | 6 | 7 | INTNO | intno | ~{M1} | T | IFF
0 | 0 | 0 | 1 | 1 | 1 | 1 | 1 | 1 | 1 | 1 | 0x5 | Z | 0 | 1 | 0
1 | 0 | 0 | 1 | 1 | 1 | 1 | 1 | 1 | 1 | 1 | 0x5 | Z | 0 | 1 | 0
2 | 0 | 0 | 1 | 1 | 1 | 1 | 1 | 1 | 1 | 1 | 0x5 | Z | 1 | 2 | 0
3 | 0 | 0 | 1 | 1 | 1 | 1 | 1 | 1 | 1 | 1 | 0x5 | Z | 1 | 2 | 0
4 | 0 | 0 | 1 | 1 | 1 | 1 | 1 | 1 | 1 | 1 | 0x5 | Z | 1 | 3 | 0
5 | 0 | 0 | 1 | 1 | 1 | 1 | 1 | 1 | 1 | 1 | 0x5 | Z | 1 | 3 | 0
6 | 0 | 0 | 1 | 1 | 1 | 1 | 1 | 1 | 1 | 1 | 0x5 | Z | 0 | 0 | 0
7 | 0 | 0 | 1 | 1 | 1 | 1 | 1 | 1 | 1 | 1 | 0x5 | Z | 0 | 0 | 0
8 | 0 | 0 | 1 | 1 | 1 | 1 | 1 | 1 | 1 | 1 | 0x5 | Z | 0 | 1 | 0
9 | 0 | 0 | 1 | 1 | 1 | 1 | 1 | 1 | 1 | 1 | 0x5 | Z | 0 | 1 | 0
10 | 0 | 0 | 1 | 1 | 1 | 1 | 1 | 1 | 1 | 1 | 0x5 | Z | 1 | 2 | 0
11 | 0 | 0 | 1 | 1 | 1 | 1 | 1 | 1 | 1 | 1 | 0x5 | Z | 1 | 2 | 0
12 | 0 | 0 | 1 | 1 | 1 | 1 | 1 | 1 | 1 | 1 | 0x5 | Z | 1 | 3 | 0
13 | 0 | 0 | 1 | 1 | 1 | 1 | 1 | 1 | 1 | 1 | 0x5 | Z | 1 | 3 | 0
14 | 0 | 0 | 1 | 1 | 1 | 1 | 1 | 1 | 1 | 1 | 0x5 | Z | 0 | 0 | 0
15 | 0 | 0 | 1 | 1 | 1 | 1 | 1 | 1 | 1 | 1 | 0x5 | Z | 0 | 0 | 0
16 | 0 | 0 | 1 | 1 | 1 | 1 | 1 | 1 | 1 | 1 | 0x5 | Z | 0 | 1 | 0
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
