damouze/SZC-1/boards/core/even_simpler_z80/even_simpler_z80.kicad_pcb

## KiCad design boards/core/even_simpler_z80/even_simpler_z80.kicad_pcb (2024-04-24)

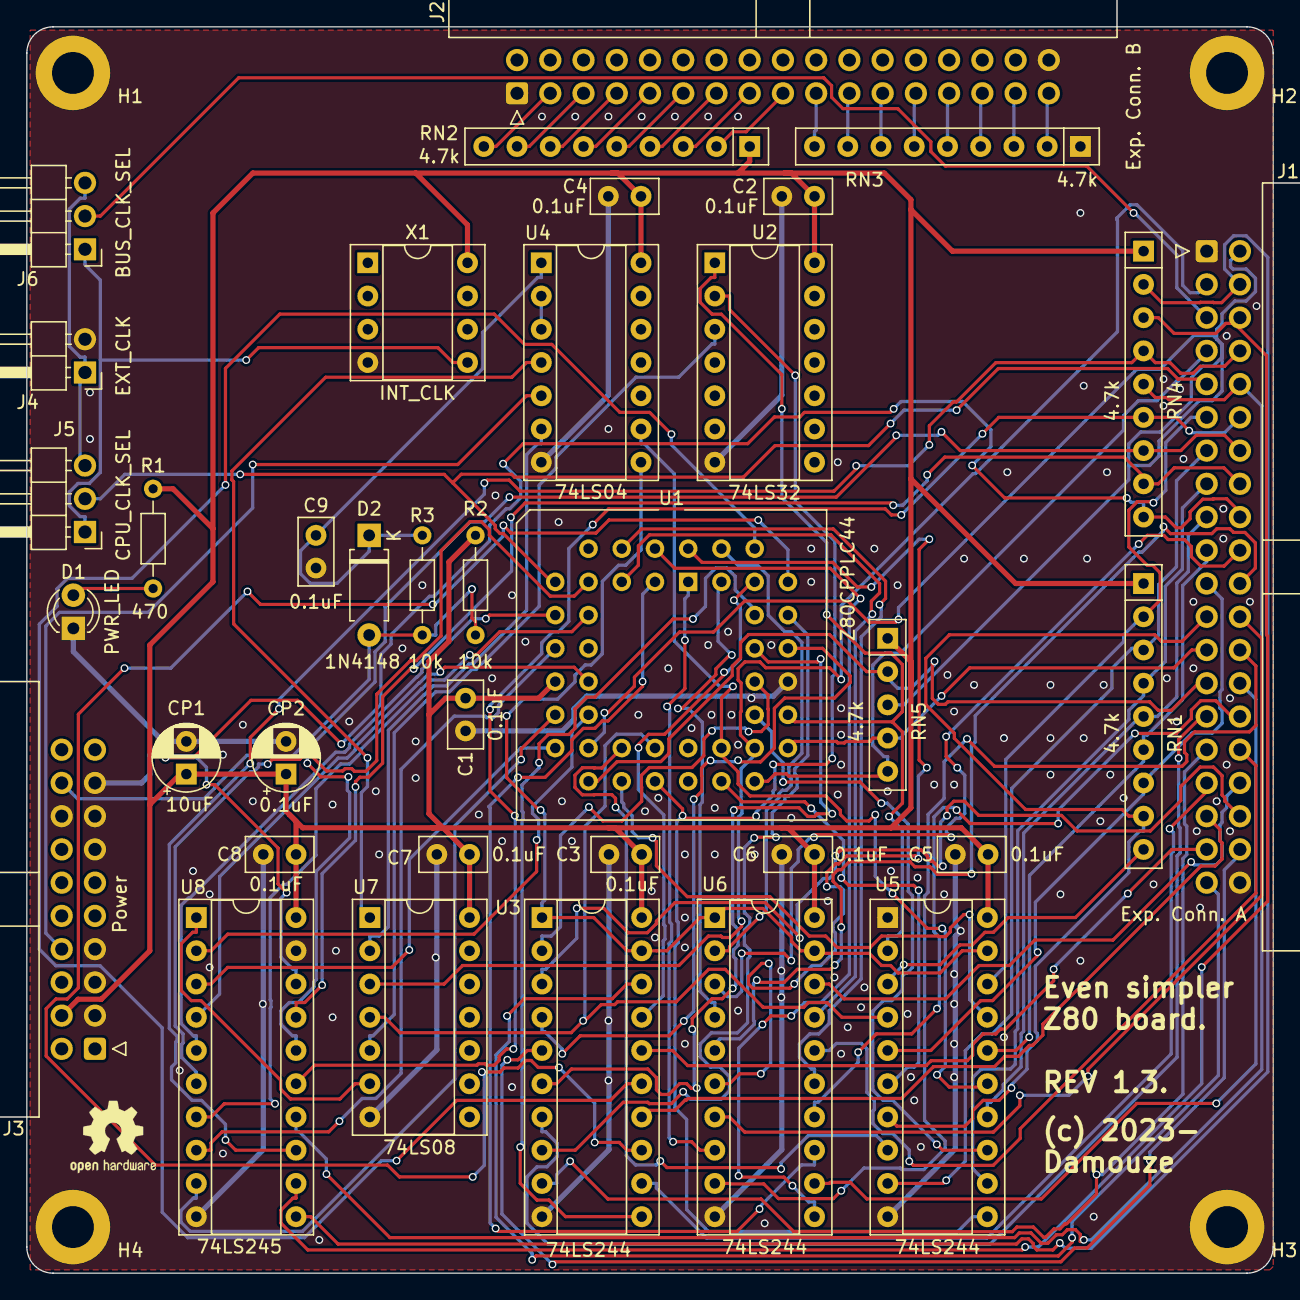
[picture p118: board even_simpler_z80.kicad_pcb from above]

Board: 2 copper layers, 95.2 x 95.2 mm, 40 parts (0 on the bottom side), 101 nets.

Parts:
C1, C2, C3, C4, C5, C6, C7, C8, C9: 0.1uF; C_Disc_D5.0mm_W2.5mm_P2.50mm
CP1: 10uF; CP_Radial_D5.0mm_P2.50mm
CP2: 0.1uF; CP_Radial_D5.0mm_P2.50mm
D1: PWR_LED; LED_D3.0mm
D2: 1N4148; D_A-405_P7.62mm_Horizontal
H1, H2, H3, H4: MountingHole_Pad; MountingHole_3.2mm_M3_ISO7380_Pad
J1: Exp. Conn. A; IDC-Header_2x20_P2.54mm_Horizontal
J2: Exp. Conn. B; IDC-Header_2x17_P2.54mm_Horizontal
J3: Power; IDC-Header_2x10_P2.54mm_Horizontal
J4: EXT_CLK; PinHeader_1x02_P2.54mm_Horizontal
J5: CPU_CLK_SEL; PinHeader_1x03_P2.54mm_Horizontal
J6: BUS_CLK_SEL; PinHeader_1x03_P2.54mm_Horizontal
R1: 470; R_Axial_DIN0204_L3.6mm_D1.6mm_P7.62mm_Horizontal
R2, R3: 10k; R_Axial_DIN0204_L3.6mm_D1.6mm_P7.62mm_Horizontal
RN1, RN2, RN3, RN4: 4.7k; R_Array_SIP9
RN5: 4.7k; R_Array_SIP5
U1: Z80CPPLC44; PLCC-44_THT-Socket
U2: 74LS32; DIP-14_W7.62mm_Socket
U3, U5, U6: 74LS244; DIP-20_W7.62mm_Socket
U4: 74LS04; DIP-14_W7.62mm_Socket
U7: 74LS08; DIP-14_W7.62mm_Socket
U8: 74LS245; DIP-20_W7.62mm_Socket
X1: INT_CLK; DIP-8_W7.62mm_Socket

Connections:
/+5V: C1.1, C2.1, C3.1, C4.1, C5.1, C6.1, C7.1, C8.1, CP1.1, CP2.1, J3.4, R1.1, R2.1, RN1.1 (common), RN2.1 (common), RN4.1 (common), RN5.1 (common), U1.13 (VCC), U2.14 (VCC), U3.20 (VCC), U4.14 (VCC), U5.20 (VCC), U6.20 (VCC), U7.14 (VCC), U8.20 (VCC), X1.8 (Vcc)
/BUS_CLK: J1.5, J6.2
/B_A0: J1.39, U3.18 (O0a)
/B_A1: J1.37, U3.16 (O1a)
/B_A2: J1.35, U3.14 (O2a)
/B_A3: J1.33, U3.12 (O3a)
/B_A4: J1.31, U3.9 (O0b)
/B_A5: J1.29, U3.7 (O1b)
/B_A6: J1.38, U3.5 (O2b)
/B_A7: J1.36, U3.3 (O3b)
/B_A8: J1.34, U6.18 (O0a)
/B_A9: J1.32, U6.16 (O1a)
/B_A10: J1.30, U6.14 (O2a)
/B_A11: J1.28, U6.12 (O3a)
/B_A12: J1.26, U6.9 (O0b)
/B_A13: J1.24, U6.7 (O1b)
/B_A14: J1.22, U6.5 (O2b)
/B_A15: J1.20, U6.3 (O3b)
/B_D0: J1.18, RN4.9 (R8), U8.18 (B0)
/B_D1: J1.16, RN4.8 (R7), U8.17 (B1)
/B_D2: J1.14, RN4.7 (R6), U8.16 (B2)
/B_D3: J1.12, RN4.6 (R5), U8.15 (B3)
/B_D4: J1.10, RN4.5 (R4), U8.14 (B4)
/B_D5: J1.8, RN4.4 (R3), U8.13 (B5)
/B_D6: J1.6, RN4.3 (R2), U8.12 (B6)
/B_D7: J1.4, RN4.2 (R1), U8.11 (B7)
/CPU_CLK: J1.9, J5.2, U1.7 (~CLK)
/Clock & Reset circuit/EXT_CLK: J4.1, J5.3, J6.3
/Clock & Reset circuit/INT_CLK: J5.1, J6.1, X1.5 (OUT)
/Clock & Reset circuit/RESET1: U4.2, U4.3
/Clock & Reset circuit/~PWR_OK: U4.6, U7.2
/Clock & Reset circuit/~RESET1: U4.4, U7.1
/Clock & Reset circuit/~RESET_IN: C9.1, D2.1 (K), R3.1, U4.1
/GND: C1.2, C2.2, C3.2, C4.2, C5.2, C6.2, C7.2, C8.2, C9.2, CP1.2, CP2.2, D1.1 (K), H1.1, H2.1, H3.1, H4.1, J1.1, J1.40, J2.1, J2.34, J3.3, J3.5, J3.7, J3.13, J3.15, J3.16, J3.17, J4.2, RN3.1 (common), U1.33 (GND), U2.7 (GND), U3.10 (GND), U4.7 (GND), U5.1 (OEa), U5.10 (GND), U6.10 (GND), U7.7 (GND), U8.10 (GND), U8.19 (CE), X1.4 (GND)
/MCU/A0: U1.34 (A0), U3.2 (I0a)
/MCU/A1: U1.35 (A1), U3.4 (I1a)
/MCU/A2: U1.36 (A2), U3.6 (I2a)
/MCU/A3: U1.37 (A3), U3.8 (I3a)
/MCU/A4: U1.38 (A4), U3.11 (I0b)
/MCU/A5: U1.39 (A5), U3.13 (I1b)
/MCU/A6: U1.40 (A6), U3.15 (I2b)
/MCU/A7: U1.41 (A7), U3.17 (I3b)
/MCU/A8: U1.42 (A8), U6.2 (I0a)
/MCU/A9: U1.43 (A9), U6.4 (I1a)
/MCU/A10: U1.44 (A10), U6.6 (I2a)
/MCU/A11: U1.1 (A11), U6.8 (I3a)
/MCU/A12: U1.2 (A12), U6.11 (I0b)
/MCU/A13: U1.3 (A13), U6.13 (I1b)
/MCU/A14: U1.4 (A14), U6.15 (I2b)
/MCU/A15: U1.5 (A15), U6.17 (I3b)
/MCU/BUSACK: U3.1 (OEa), U3.19 (OEb), U4.8, U5.19 (OEb), U6.1 (OEa), U6.19 (OEb)
/MCU/D0: U1.16 (D0), U8.2 (A0)
/MCU/D1: U1.17 (D1), U8.3 (A1)
/MCU/D2: U1.14 (D2), U8.4 (A2)
/MCU/D3: U1.9 (D3), U8.5 (A3)
/MCU/D4: U1.8 (D4), U8.6 (A4)
/MCU/D5: U1.10 (D5), U8.7 (A5)
/MCU/D6: U1.11 (D6), U8.8 (A6)
/MCU/D7: U1.15 (D7), U8.9 (A7)
/MCU/~BUSACK: U1.27 (~BUSACK), U4.9, U5.15 (I2b)
/MCU/~BUSDIR: U7.6, U8.1 (A->B)
/MCU/~HALT: U1.20 (~HALT), U5.17 (I3b)
/MCU/~IORQ: U1.22 (~IORQ), U2.2, U5.11 (I0b)
/MCU/~M1: U1.31 (~M1), U2.1, U5.2 (I0a)
/MCU/~MREQ: U1.21 (~MREQ), U5.8 (I3a)
/MCU/~RD: U1.23 (~RD), U5.4 (I1a), U7.4
/MCU/~RFSH: U1.32 (~RFSH), U5.13 (I1b)
/MCU/~WR: U1.26 (~WR), U5.6 (I2a)
/M_A14: J2.33, RN3.2 (R1)
/M_A15: J2.31, RN3.3 (R2)
/M_A16: J2.29, RN3.4 (R3)
/M_A17: J2.27, RN3.5 (R4)
/M_A18: J2.25, RN3.6 (R5)
/M_A19: J2.23, RN3.7 (R6)
/M_A20: J2.21, RN3.8 (R7)
/M_A21: J2.19, RN3.9 (R8)
/PWR_OK: J3.8, U4.5
/~BUSREQ: J1.25, RN5.4 (R3), U1.29 (~BUSRQ)
/~B_BUSACK: J1.21, RN1.7 (R6), U5.5 (O2b)
/~B_HALT: RN1.9 (R8), U5.3 (O3b)
/~B_IORQ: J1.13, RN1.3 (R2), U5.9 (O0b)
/~B_M1: J1.11, RN1.2 (R1), U5.18 (O0a)
/~B_MREQ: J1.15, RN1.4 (R3), U5.12 (O3a)
/~B_RD: J1.19, RN1.6 (R5), U5.16 (O1a)
/~B_RFSH: J1.23, RN1.8 (R7), U5.7 (O1b)
/~B_WR: J1.17, RN1.5 (R4), U5.14 (O2a)
/~INT0: J2.17, RN2.2 (R1)
/~INT1: J2.15, RN2.3 (R2)
/~INT2: J2.13, RN2.4 (R3)
/~INT3: J2.11, RN2.5 (R4)
/~INT4: J2.9, RN2.6 (R5)
/~INT5: J2.7, RN2.7 (R6)
/~INT6: J2.5, RN2.8 (R7)
/~INT7: J2.3, RN2.9 (R8)
/~INTA: U2.3, U7.5
/~INT: J1.27, RN5.2 (R1), U1.18 (~INT)
/~NMI: J1.2, RN5.3 (R2), U1.19 (~NMI)
/~RESET_SW: D2.2 (A), J3.18, R2.2, R3.2
/~RESET: J1.3, U1.30 (~RESET), U7.3
/~WAIT: J1.7, RN5.5 (R4), U1.28 (~WAIT)
unnamed: D1.2 (A), R1.2
