damouze/SZC-1/boards/extra/rom_ram_board_128kB_v2/rom_ram_board_128kB_v2.kicad_pcb

## KiCad design boards/extra/rom_ram_board_128kB_v2/rom_ram_board_128kB_v2.kicad_pcb (2024-04-24)

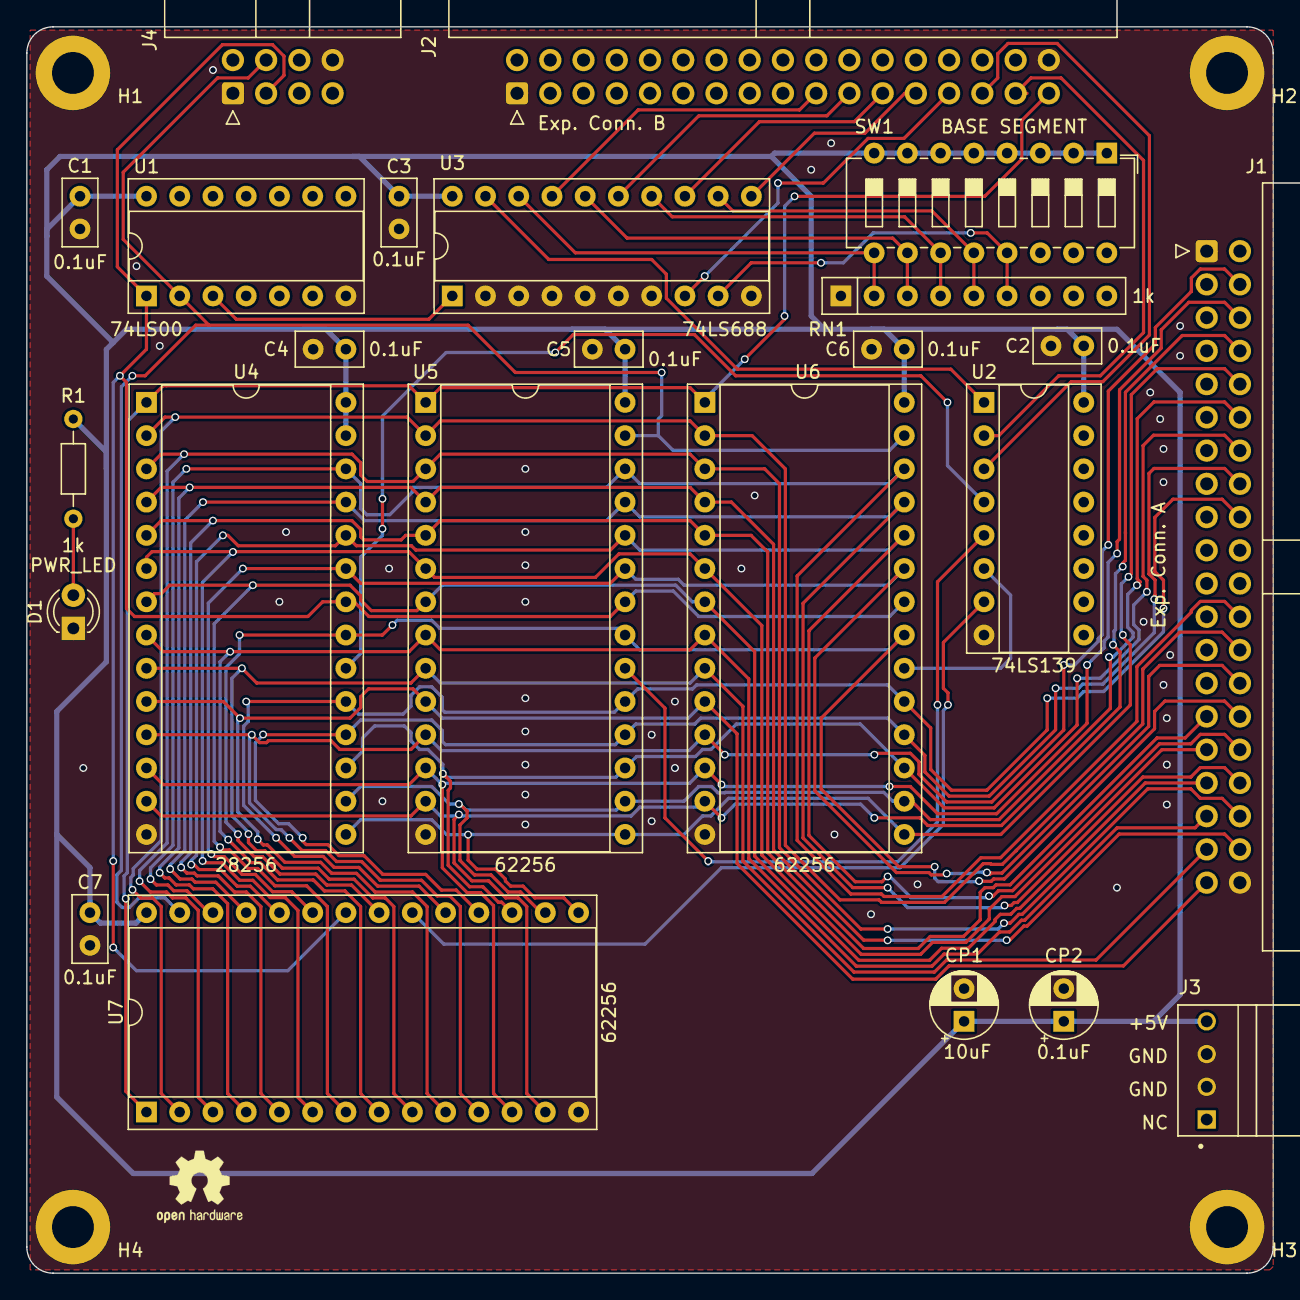
[picture p119: board rom_ram_board_128kB_v2.kicad_pcb from above]

Board: 2 copper layers, 95.2 x 95.2 mm, 28 parts (0 on the bottom side), 46 nets.

Parts:
C1, C2, C3, C4, C5, C6, C7: 0.1uF; C_Disc_D5.0mm_W2.5mm_P2.50mm
CP1: 10uF; CP_Radial_D5.0mm_P2.50mm
CP2: 0.1uF; CP_Radial_D5.0mm_P2.50mm
D1: PWR_LED; LED_D3.0mm
H1, H2, H3, H4: MountingHole_Pad; MountingHole_3.2mm_M3_ISO7380_Pad
J1: Exp. Conn. A; IDC-Header_2x20_P2.54mm_Horizontal
J2: Exp. Conn. B; IDC-Header_2x17_P2.54mm_Horizontal
J3: Power; TE_171826-4
J4: Exp. Conn. C; IDC-Header_2x04_P2.54mm_Horizontal
R1: 1k; R_Axial_DIN0204_L3.6mm_D1.6mm_P7.62mm_Horizontal
RN1: 1k; R_Array_SIP9
SW1: BASE SEGMENT; SW_DIP_SPSTx08_Slide_6.7x21.88mm_W7.62mm_P2.54mm_LowProfile
U1: 74LS00; DIP-14_W7.62mm_Socket
U2: 74LS139; DIP-16_W7.62mm_Socket
U3: 74LS688; DIP-20_W7.62mm_Socket
U4: 28256; DIP-28_W15.24mm_Socket
U5, U6, U7: 62256; DIP-28_W15.24mm_Socket

Connections:
/+5V: C1.1, C2.1, C3.1, C4.1, C5.1, C6.1, C7.1, CP1.1, CP2.1, J3.4, R1.1, SW1.1, SW1.2, SW1.3, SW1.4, SW1.5, SW1.6, SW1.7, SW1.8, U1.14 (VCC), U2.16 (VCC), U3.20 (VCC), U4.27 (~WE), U4.28 (VCC), U5.28 (VCC), U6.28 (VCC), U7.28 (VCC)
/B_A0: J1.39, U4.10 (A0), U5.10 (A0), U6.10 (A0), U7.10 (A0)
/B_A1: J1.37, U4.9 (A1), U5.9 (A1), U6.9 (A1), U7.9 (A1)
/B_A2: J1.35, U4.8 (A2), U5.8 (A2), U6.8 (A2), U7.8 (A2)
/B_A3: J1.33, U4.7 (A3), U5.7 (A3), U6.7 (A3), U7.7 (A3)
/B_A4: J1.31, U4.6 (A4), U5.6 (A4), U6.6 (A4), U7.6 (A4)
/B_A5: J1.29, U4.5 (A5), U5.5 (A5), U6.5 (A5), U7.5 (A5)
/B_A6: J1.38, U4.4 (A6), U5.4 (A6), U6.4 (A6), U7.4 (A6)
/B_A7: J1.36, U4.3 (A7), U5.3 (A7), U6.3 (A7), U7.3 (A7)
/B_A8: J1.34, U4.25 (A8), U5.25 (A8), U6.25 (A8), U7.25 (A8)
/B_A9: J1.32, U4.24 (A9), U5.24 (A9), U6.24 (A9), U7.24 (A9)
/B_A10: J1.30, U4.21 (A10), U5.21 (A10), U6.21 (A10), U7.21 (A10)
/B_A11: J1.28, U4.23 (A11), U5.23 (A11), U6.23 (A11), U7.23 (A11)
/B_A12: J1.26, U4.2 (A12), U5.2 (A12), U6.2 (A12), U7.2 (A12)
/B_A13: J1.24, U4.26 (A13), U5.26 (A13), U6.26 (A13), U7.26 (A13)
/B_D0: J1.18, U4.19 (D7), U5.19 (Q7), U6.19 (Q7), U7.19 (Q7)
/B_D1: J1.16, U4.18 (D6), U5.18 (Q6), U6.18 (Q6), U7.18 (Q6)
/B_D2: J1.14, U4.17 (D5), U5.17 (Q5), U6.17 (Q5), U7.17 (Q5)
/B_D3: J1.12, U4.16 (D4), U5.16 (Q4), U6.16 (Q4), U7.16 (Q4)
/B_D4: J1.10, U4.15 (D3), U5.15 (Q3), U6.15 (Q3), U7.15 (Q3)
/B_D5: J1.8, U4.13 (D2), U5.13 (Q2), U6.13 (Q2), U7.13 (Q2)
/B_D6: J1.6, U4.12 (D1), U5.12 (Q1), U6.12 (Q1), U7.12 (Q1)
/B_D7: J1.4, U4.11 (D0), U5.11 (Q0), U6.11 (Q0), U7.11 (Q0)
/GND: C1.2, C2.2, C3.2, C4.2, C5.2, C6.2, C7.2, CP1.2, CP2.2, D1.1 (K), H1.1, H2.1, H3.1, H4.1, J1.1, J1.40, J2.1, J2.34, J3.2, J3.3, J4.1, J4.8, RN1.1 (common), U1.7 (GND), U2.8 (GND), U3.2 (P0), U3.3 (R0), U3.4 (P1), U3.5 (R1), U3.6 (P2), U3.7 (R2), U3.10 (GND), U4.14 (GND), U5.14 (GND), U6.14 (GND), U7.14 (GND)
/M_A14: J2.33, U4.1 (A14), U5.1 (A14), U6.1 (A14), U7.1 (A14)
/M_A15: J2.31, U2.2 (A0)
/M_A16: J2.29, U2.3 (A1)
/M_A17: J2.27, U3.8 (P3)
/M_A18: J2.25, U3.11 (P4)
/M_A19: J2.23, U3.13 (P5)
/M_A20: J2.21, U3.15 (P6)
/M_A21: J2.19, U3.17 (P7)
/R_A17: RN1.6 (R5), SW1.13, U3.9 (R3)
/R_A18: RN1.5 (R4), SW1.12, U3.12 (R4)
/R_A19: RN1.4 (R3), SW1.11, U3.14 (R5)
/R_A20: RN1.3 (R2), SW1.10, U3.16 (R6)
/R_A21: RN1.2 (R1), SW1.9, U3.18 (R7)
/~MEMR: J4.3, U1.1, U4.22 (~OE), U5.22 (~OE), U6.22 (~OE), U7.22 (~OE)
/~MEMW: J4.4, U1.2, U5.27 (~WE), U6.27 (~WE), U7.27 (~WE)
/~MEMXS: U1.3, U3.1 (G)
/~MEM_CS1: U2.4 (O0), U4.20 (~CS)
/~MEM_CS2: U2.5 (O1), U5.20 (~CS)
/~MEM_CS3: U2.6 (O2), U6.20 (~CS)
/~MEM_CS4: U2.7 (O3), U7.20 (~CS)
/~MEM_CS: U2.1 (E), U3.19 (P=R)
unnamed: D1.2 (A), R1.2
