damouze/SZC-1/boards/msx_compat/ppi_slot_select/ppi_slot_select.kicad_pcb

## KiCad design boards/msx_compat/ppi_slot_select/ppi_slot_select.kicad_pcb (2023-12-30)

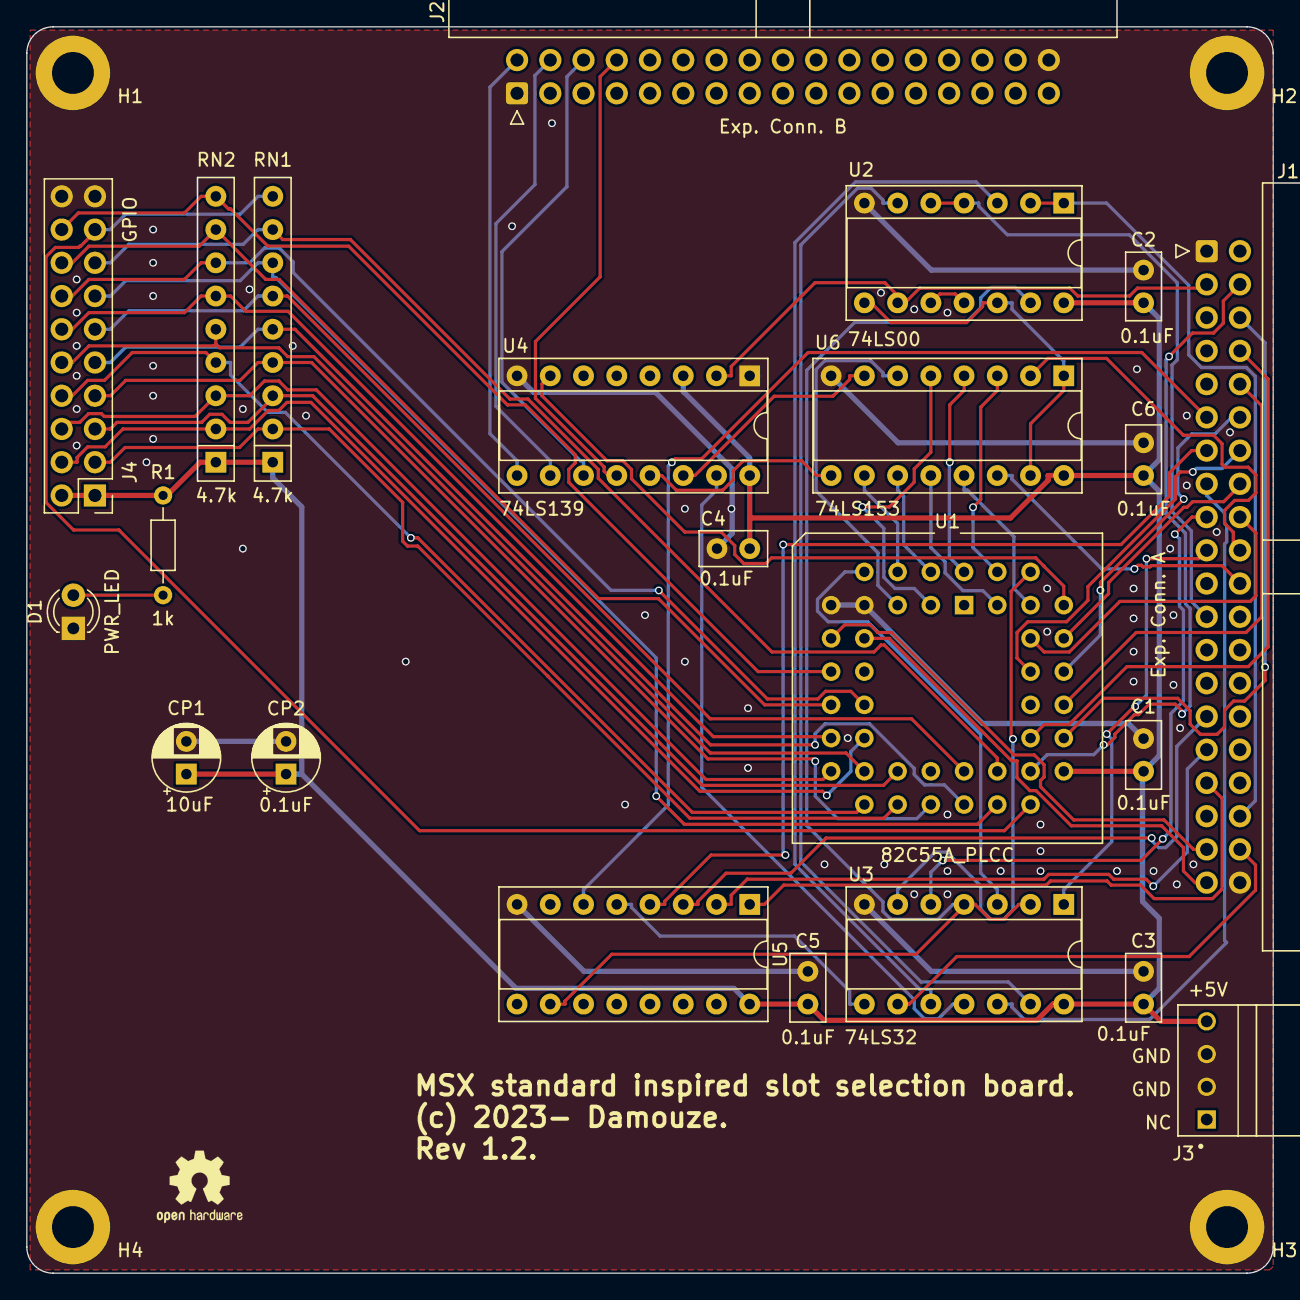
[picture p120: board ppi_slot_select.kicad_pcb from above]

Board: 2 copper layers, 95.2 x 95.2 mm, 26 parts (0 on the bottom side), 67 nets.

Parts:
C1, C2, C3, C4, C5, C6: 0.1uF; C_Disc_D5.0mm_W2.5mm_P2.50mm
CP1: 10uF; CP_Radial_D5.0mm_P2.50mm
CP2: 0.1uF; CP_Radial_D5.0mm_P2.50mm
D1: PWR_LED; LED_D3.0mm
H1, H2, H3, H4: MountingHole_Pad; MountingHole_3.2mm_M3_ISO7380_Pad
J1: Exp. Conn. A; IDC-Header_2x20_P2.54mm_Horizontal
J2: Exp. Conn. B; IDC-Header_2x17_P2.54mm_Horizontal
J3: Power; TE_171826-4
J4: GPIO; PinHeader_2x10_P2.54mm_Vertical
R1: 1k; R_Axial_DIN0204_L3.6mm_D1.6mm_P7.62mm_Horizontal
RN1, RN2: 4.7k; R_Array_SIP9
U1: 82C55A_PLCC; PLCC-44_THT-Socket
U2: 74LS00; DIP-14_W7.62mm_Socket
U3: 74LS32; DIP-14_W7.62mm_Socket
U4: 74LS139; DIP-16_W7.62mm_Socket
U5: 74LS138; DIP-16_W7.62mm_Socket
U6: 74LS153; DIP-16_W7.62mm_Socket

Connections:
/+5V: C1.1, C2.1, C3.1, C4.1, C5.1, C6.1, CP1.1, CP2.1, J3.4, J4.1, J4.2, R1.1, RN1.1 (common), RN2.1 (common), U1.29 (VCC), U2.14 (VCC), U3.14 (VCC), U4.3 (A1), U4.16 (VCC), U5.16 (VCC), U6.16 (VCC)
/B_A0: J1.39, U1.10 (A0)
/B_A1: J1.37, U1.9 (A1)
/B_A3: J1.33, U5.1 (A0)
/B_A4: J1.31, U5.2 (A1)
/B_A5: J1.29, U5.3 (A2)
/B_A6: J1.38, U3.9
/B_A7: J1.36, U2.1, U2.2
/B_A14: J1.22, U6.14 (S0)
/B_A15: J1.20, U6.2 (S1)
/B_D0: J1.18, U1.38 (D0)
/B_D1: J1.16, U1.37 (D1)
/B_D2: J1.14, U1.36 (D2)
/B_D3: J1.12, U1.35 (D3)
/B_D4: J1.10, U1.33 (D4)
/B_D5: J1.8, U1.32 (D5)
/B_D6: J1.6, U1.31 (D6)
/B_D7: J1.4, U1.30 (D7)
/GND: C1.2, C2.2, C3.2, C4.2, C5.2, C6.2, CP1.2, CP2.2, D1.1 (K), H1.1, H2.1, H3.1, H4.1, J1.1, J1.40, J2.1, J2.34, J3.2, J3.3, J4.19, J4.20, U1.7 (~CS), U1.8 (GND), U2.7 (GND), U3.7 (GND), U4.1 (E), U4.8 (GND), U5.8 (GND), U6.8 (GND)
/PB0: J4.3, RN1.2 (R1), U1.20 (PB0)
/PB1: J4.5, RN1.3 (R2), U1.21 (PB1)
/PB2: J4.7, RN1.4 (R3), U1.22 (PB2)
/PB3: J4.9, RN1.5 (R4), U1.24 (PB3)
/PB4: J4.11, RN1.6 (R5), U1.25 (PB4)
/PB5: J4.13, RN1.7 (R6), U1.26 (PB5)
/PB6: J4.15, RN1.8 (R7), U1.27 (PB6)
/PB7: J4.17, RN1.9 (R8), U1.28 (PB7)
/PC0: J4.4, RN2.2 (R1), U1.16 (PC0)
/PC1: J4.6, RN2.3 (R2), U1.17 (PC1)
/PC2: J4.8, RN2.4 (R3), U1.18 (PC2)
/PC3: J4.10, RN2.5 (R4), U1.19 (PC3)
/PC4: J4.12, RN2.6 (R5), U1.15 (PC4)
/PC5: J4.14, RN2.7 (R6), U1.14 (PC5)
/PC6: J4.16, RN2.8 (R7), U1.13 (PC6)
/PC7: J4.18, RN2.9 (R8), U1.11 (PC7)
/RESET: U1.39 (RESET), U4.7 (O3)
/Y5: U2.13, U3.2, U3.4, U5.10 (O5)
/~B_IORQ: J1.13, U5.4 (E1)
/~B_M1: J1.11, U5.6 (E3)
/~B_MREQ: J1.15, U3.12
/~B_RD: J1.19, U3.1
/~B_RFSH: J1.23, U2.4, U2.5
/~B_WR: J1.17, U3.5
/~CS0H: U1.4 (PA1), U6.10 (I0b)
/~CS0L: U1.5 (PA0), U6.6 (I0a)
/~CS1H: U1.2 (PA3), U6.11 (I1b)
/~CS1L: U1.3 (PA2), U6.5 (I1a)
/~CS2H: U1.43 (PA5), U6.12 (I2b)
/~CS2L: U1.44 (PA4), U6.4 (I2a)
/~CS3H: U1.41 (PA7), U6.13 (I3b)
/~CS3L: U1.42 (PA6), U6.3 (I3a)
/~PPI_RD: U1.6 (~RD), U3.3
/~PPI_WR: U1.40 (~WR), U3.6
/~RESET: J1.3, U2.9, U4.2 (A0)
/~SLTSL0: J2.8, U4.12 (O0)
/~SLTSL1: J2.6, U4.11 (O1)
/~SLTSL2: J2.4, U4.10 (O2)
/~SLTSL3: J2.2, U4.9 (O3)
unnamed: D1.2 (A), R1.2
unnamed: U2.3, U3.10
unnamed: U2.6, U3.13
unnamed: U2.10, U2.11
unnamed: U4.14 (A0), U6.7 (Za)
unnamed: U4.13 (A1), U6.9 (Zb)
unnamed: U3.11, U4.15 (E)
unnamed: U3.8, U5.5 (E2)
unnamed: U2.8, U2.12, U6.1 (Ea), U6.15 (Eb)
