damouze/SZC-1/boards/core/rom_ram_board/rom_ram_board.kicad_pcb

## KiCad design boards/core/rom_ram_board/rom_ram_board.kicad_pcb (2023-12-30)

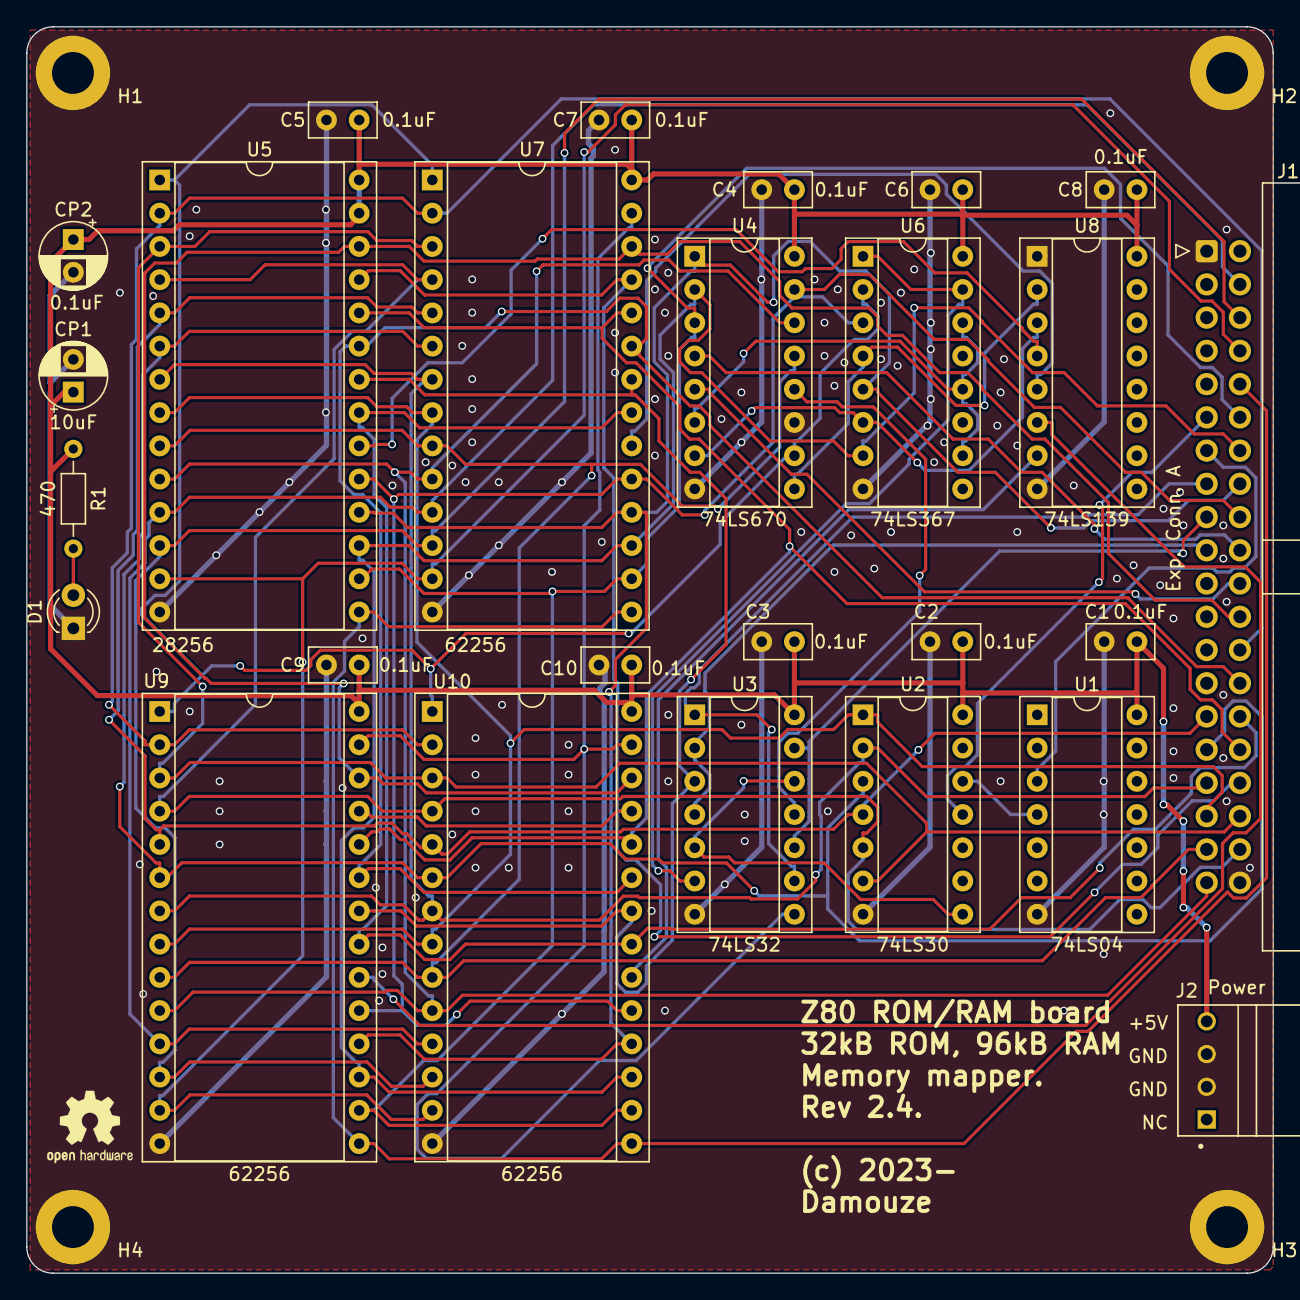
[picture p121: board rom_ram_board.kicad_pcb from above]

Board: 2 copper layers, 95.2 x 95.2 mm, 30 parts (0 on the bottom side), 46 nets.

Parts:
C1, C2, C3, C4, C5, C6, C7, C8, C9, C10: 0.1uF; C_Disc_D5.0mm_W2.5mm_P2.50mm
CP1: 10uF; CP_Radial_D5.0mm_P2.50mm
CP2: 0.1uF; CP_Radial_D5.0mm_P2.50mm
D1: PWR_LED; LED_D3.0mm
H1, H2, H3, H4: MountingHole_Pad; MountingHole_3.2mm_M3_ISO7380_Pad
J1: Exp. Conn. A; IDC-Header_2x20_P2.54mm_Horizontal
J2: Power; TE_171826-4
R1: 470; R_Axial_DIN0204_L3.6mm_D1.6mm_P7.62mm_Horizontal
U1: 74LS04; DIP-14_W7.62mm_Socket
U2: 74LS30; DIP-14_W7.62mm_Socket
U3: 74LS32; DIP-14_W7.62mm_Socket
U4: 74LS670; DIP-16_W7.62mm_Socket
U5: 28256; DIP-28_W15.24mm_Socket
U6: 74LS367; DIP-16_W7.62mm_Socket
U7, U9, U10: 62256; DIP-28_W15.24mm_Socket
U8: 74LS139; DIP-16_W7.62mm_Socket

Connections:
/+5V: C1.1, C2.1, C3.1, C4.1, C5.1, C6.1, C7.1, C8.1, C9.1, C10.1, CP1.1, CP2.1, J2.4, R1.1, U1.14 (VCC), U2.14 (VCC), U3.14 (VCC), U4.16 (VCC), U5.27 (~WE), U5.28 (VCC), U6.16 (VCC), U7.28 (VCC), U8.16 (VCC), U9.28 (VCC), U10.28 (VCC)
/B_A0: J1.39, U4.14 (Wa), U5.10 (A0), U7.10 (A0), U9.10 (A0), U10.10 (A0)
/B_A1: J1.37, U4.13 (Wb), U5.9 (A1), U7.9 (A1), U9.9 (A1), U10.9 (A1)
/B_A2: J1.35, U2.1, U5.8 (A2), U7.8 (A2), U9.8 (A2), U10.8 (A2)
/B_A3: J1.33, U2.2, U5.7 (A3), U7.7 (A3), U9.7 (A3), U10.7 (A3)
/B_A4: J1.31, U2.3, U5.6 (A4), U7.6 (A4), U9.6 (A4), U10.6 (A4)
/B_A5: J1.29, U2.4, U5.5 (A5), U7.5 (A5), U9.5 (A5), U10.5 (A5)
/B_A6: J1.38, U2.5, U5.4 (A6), U7.4 (A6), U9.4 (A6), U10.4 (A6)
/B_A7: J1.36, U2.6, U5.3 (A7), U7.3 (A7), U9.3 (A7), U10.3 (A7)
/B_A8: J1.34, U5.25 (A8), U7.25 (A8), U9.25 (A8), U10.25 (A8)
/B_A9: J1.32, U5.24 (A9), U7.24 (A9), U9.24 (A9), U10.24 (A9)
/B_A10: J1.30, U5.21 (A10), U7.21 (A10), U9.21 (A10), U10.21 (A10)
/B_A11: J1.28, U5.23 (A11), U7.23 (A11), U9.23 (A11), U10.23 (A11)
/B_A12: J1.26, U5.2 (A12), U7.2 (A12), U9.2 (A12), U10.2 (A12)
/B_A13: J1.24, U5.26 (A13), U7.26 (A13), U9.26 (A13), U10.26 (A13)
/B_A14: J1.22, U4.5 (Ra)
/B_A15: J1.20, U4.4 (Rb)
/B_D0: J1.18, U4.15 (D1), U5.19 (D7), U6.3 (O1a), U7.19 (Q7), U9.19 (Q7), U10.19 (Q7)
/B_D1: J1.16, U4.1 (D2), U5.18 (D6), U6.5 (O2a), U7.18 (Q6), U9.18 (Q6), U10.18 (Q6)
/B_D2: J1.14, U4.2 (D3), U5.17 (D5), U6.7 (O3a), U7.17 (Q5), U9.17 (Q5), U10.17 (Q5)
/B_D3: J1.12, U4.3 (D4), U5.16 (D4), U7.16 (Q4), U9.16 (Q4), U10.16 (Q4)
/B_D4: J1.10, U5.15 (D3), U7.15 (Q3), U9.15 (Q3), U10.15 (Q3)
/B_D5: J1.8, U5.13 (D2), U7.13 (Q2), U9.13 (Q2), U10.13 (Q2)
/B_D6: J1.6, U5.12 (D1), U7.12 (Q1), U9.12 (Q1), U10.12 (Q1)
/B_D7: J1.4, U5.11 (D0), U7.11 (Q0), U9.11 (Q0), U10.11 (Q0)
/GND: C1.2, C2.2, C3.2, C4.2, C5.2, C6.2, C7.2, C8.2, C9.2, C10.2, CP1.2, CP2.2, D1.1 (K), H1.1, H2.1, H3.1, H4.1, J1.1, J1.40, J2.2, J2.3, U1.7 (GND), U2.7 (GND), U3.7 (GND), U4.8 (GND), U4.11 (~Er), U5.14 (GND), U6.8 (GND), U7.14 (GND), U8.1 (E), U8.8 (GND), U9.14 (GND), U10.14 (GND)
/IORQ: U1.4, U2.12
/R_A14: U4.10 (Q1), U5.1 (A14), U6.2 (I1), U7.1 (A14), U9.1 (A14), U10.1 (A14)
/R_A15: U4.9 (Q2), U6.4 (I2), U8.2 (A0)
/R_A16: U4.7 (Q3), U6.6 (I3), U8.3 (A1)
/~B_IORQ: J1.13, U1.3
/~B_M1: J1.11, U2.11
/~B_MREQ: J1.15, U3.1, U3.9
/~B_RD: J1.19, U3.2, U3.4
/~B_WR: J1.17, U3.10, U3.13
/~IO_RD: U3.6, U6.1 (OEa), U6.15 (OEb)
/~IO_WR: U3.11, U4.12 (~Ew)
/~MM_RD: U3.3, U5.22 (~OE), U7.22 (~OE), U9.22 (~OE), U10.22 (~OE)
/~MM_WR: U3.8, U7.27 (~WE), U9.27 (~WE), U10.27 (~WE)
/~RAM1_CS: U7.20 (~CS), U8.5 (O1)
/~RAM2_CS: U8.6 (O2), U9.20 (~CS)
/~RAM3_CS: U8.7 (O3), U10.20 (~CS)
/~ROM_CS: U5.20 (~CS), U8.4 (O0)
unnamed: D1.2 (A), R1.2
unnamed: U2.8, U3.5, U3.12
unnamed: U4.6 (Q4), U6.10 (I4), U6.12 (I5), U6.14 (I6)
