damouze/SZC-1/boards/msx_compat/ppi_slot_select_expanded/ppi_slot_select_expanded.kicad_pcb

## KiCad design boards/msx_compat/ppi_slot_select_expanded/ppi_slot_select_expanded.kicad_pcb (2023-12-30)

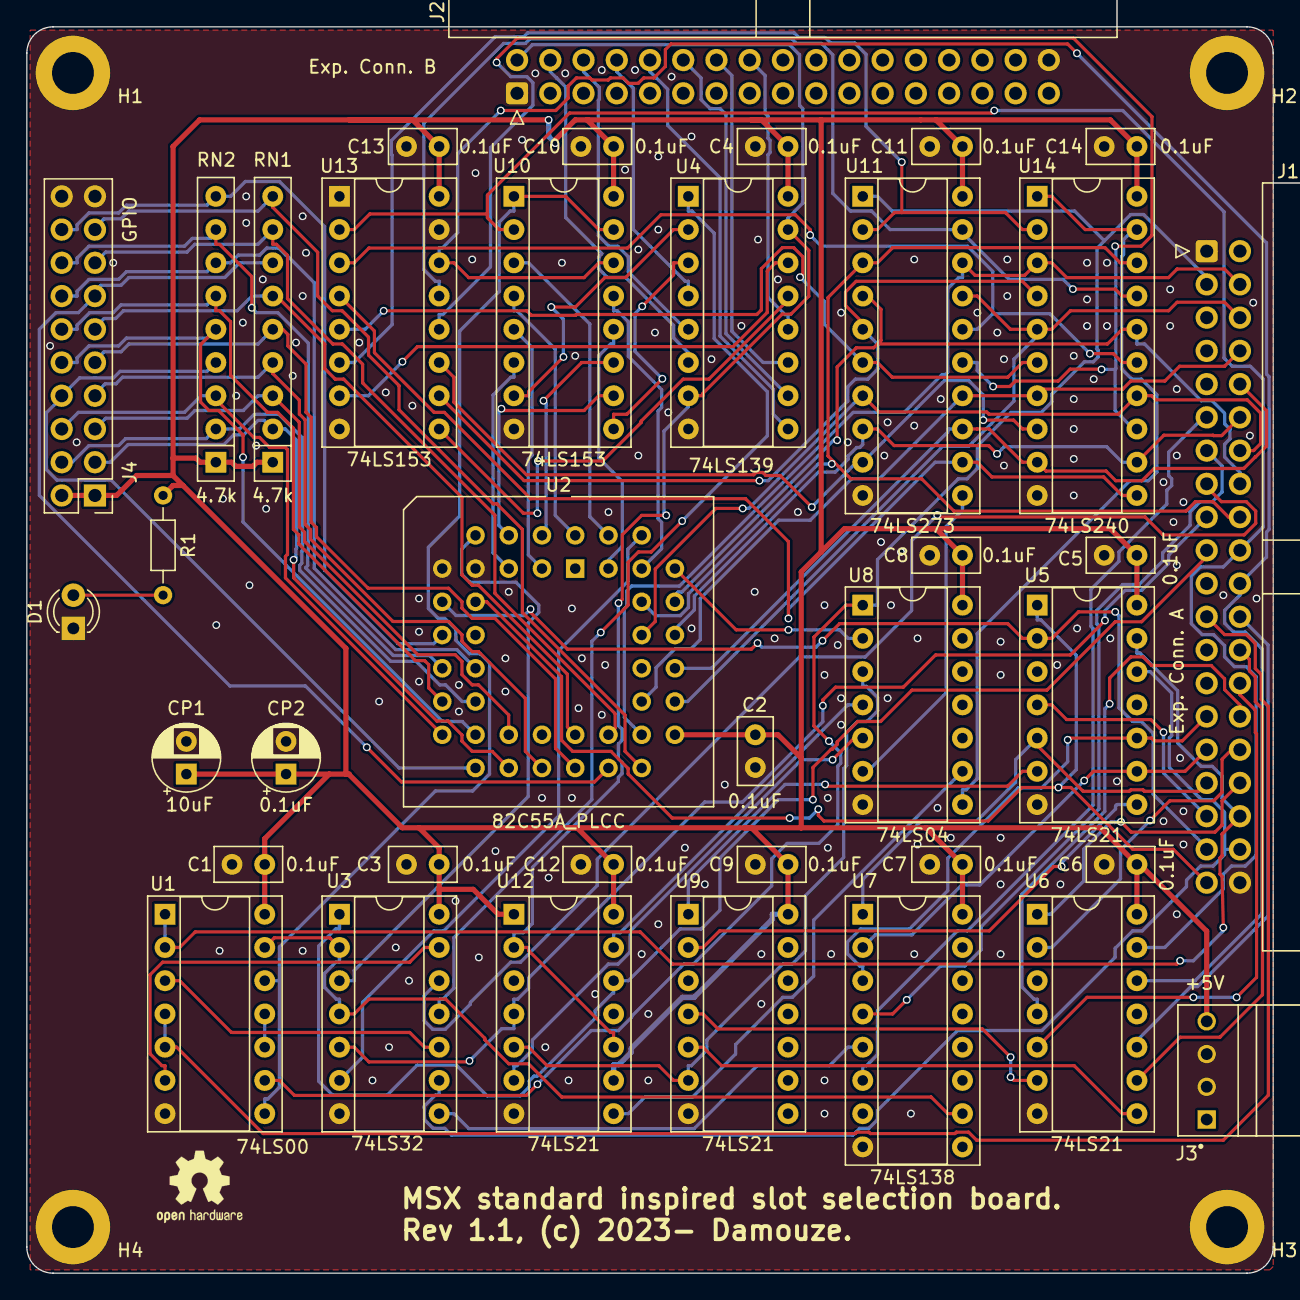
[picture p122: board ppi_slot_select_expanded.kicad_pcb from above]

Board: 2 copper layers, 95.2 x 95.2 mm, 42 parts (0 on the bottom side), 98 nets.

Parts:
C1, C2, C3, C4, C5, C6, C7, C8, C9, C10, C11, C12, C13, C14: 0.1uF; C_Disc_D5.0mm_W2.5mm_P2.50mm
CP1: 10uF; CP_Radial_D5.0mm_P2.50mm
CP2: 0.1uF; CP_Radial_D5.0mm_P2.50mm
D1: PWR_LED; LED_D3.0mm
H1, H2, H3, H4: MountingHole_Pad; MountingHole_3.2mm_M3_ISO7380_Pad
J1: Exp. Conn. A; IDC-Header_2x20_P2.54mm_Horizontal
J2: Exp. Conn. B; IDC-Header_2x17_P2.54mm_Horizontal
J3: Power; TE_171826-4
J4: GPIO; PinHeader_2x10_P2.54mm_Vertical
R1: 470; R_Axial_DIN0204_L3.6mm_D1.6mm_P7.62mm_Horizontal
RN1, RN2: 4.7k; R_Array_SIP9
U1: 74LS00; DIP-14_W7.62mm_Socket
U2: 82C55A_PLCC; PLCC-44_THT-Socket
U3: 74LS32; DIP-14_W7.62mm_Socket
U4: 74LS139; DIP-16_W7.62mm_Socket
U5, U6, U9, U12: 74LS21; DIP-14_W7.62mm_Socket
U7: 74LS138; DIP-16_W7.62mm_Socket
U8: 74LS04; DIP-14_W7.62mm_Socket
U10, U13: 74LS153; DIP-16_W7.62mm_Socket
U11: 74LS273; DIP-20_W7.62mm_Socket
U14: 74LS240; DIP-20_W7.62mm_Socket

Connections:
/#FFFF: U8.3, U9.6, U12.5
/+5V: C1.1, C2.1, C3.1, C4.1, C5.1, C6.1, C7.1, C8.1, C9.1, C10.1, C11.1, C12.1, C13.1, C14.1, CP1.1, CP2.1, J3.4, J4.1, J4.2, R1.1, RN1.1 (common), RN2.1 (common), U1.14 (VCC), U2.29 (VCC), U3.14 (VCC), U4.16 (VCC), U5.14 (VCC), U6.14 (VCC), U7.16 (VCC), U8.14 (VCC), U9.14 (VCC), U10.16 (VCC), U11.20 (VCC), U12.1, U12.9, U12.14 (VCC), U13.16 (VCC), U14.20 (VCC)
/B_A0: J1.39, U2.10 (A0), U5.1
/B_A1: J1.37, U2.9 (A1), U5.2
/B_A2: J1.35, U5.4
/B_A3: J1.33, U5.5, U7.1 (A0)
/B_A4: J1.31, U5.9, U7.2 (A1)
/B_A5: J1.29, U5.10, U7.3 (A2)
/B_A6: J1.38, U3.9, U5.12
/B_A7: J1.36, U1.1, U1.2, U5.13
/B_A8: J1.34, U6.1
/B_A9: J1.32, U6.2
/B_A10: J1.30, U6.4
/B_A11: J1.28, U6.5
/B_A12: J1.26, U6.9
/B_A13: J1.24, U6.10
/B_A14: J1.22, U6.12, U10.14 (S0), U13.14 (S0)
/B_A15: J1.20, U6.13, U10.2 (S1), U13.2 (S1)
/B_D0: J1.18, U2.38 (D0), U11.3 (D0), U14.18 (O0a)
/B_D1: J1.16, U2.37 (D1), U11.4 (D1), U14.16 (O1a)
/B_D2: J1.14, U2.36 (D2), U11.7 (D2), U14.14 (O2a)
/B_D3: J1.12, U2.35 (D3), U11.8 (D3), U14.12 (O3a)
/B_D4: J1.10, U2.33 (D4), U11.13 (D4), U14.9 (O0b)
/B_D5: J1.8, U2.32 (D5), U11.14 (D5), U14.7 (O1b)
/B_D6: J1.6, U2.31 (D6), U11.17 (D6), U14.5 (O2b)
/B_D7: J1.4, U2.30 (D7), U11.18 (D7), U14.3 (O3b)
/GND: C1.2, C2.2, C3.2, C4.2, C5.2, C6.2, C7.2, C8.2, C9.2, C10.2, C11.2, C12.2, C13.2, C14.2, CP1.2, CP2.2, D1.1 (K), H1.1, H2.1, H3.1, H4.1, J1.1, J1.40, J2.1, J2.34, J3.2, J3.3, J4.19, J4.20, U1.7 (GND), U2.7 (~CS), U2.8 (GND), U3.7 (GND), U4.8 (GND), U5.7 (GND), U6.7 (GND), U7.8 (GND), U8.7 (GND), U9.7 (GND), U10.8 (GND), U11.10 (GND), U12.7 (GND), U13.1 (Ea), U13.8 (GND), U13.15 (Eb), U14.10 (GND)
/PB0: J4.3, RN1.2 (R1), U2.20 (PB0)
/PB1: J4.5, RN1.3 (R2), U2.21 (PB1)
/PB2: J4.7, RN1.4 (R3), U2.22 (PB2)
/PB3: J4.9, RN1.5 (R4), U2.24 (PB3)
/PB4: J4.11, RN1.6 (R5), U2.25 (PB4)
/PB5: J4.13, RN1.7 (R6), U2.26 (PB5)
/PB6: J4.15, RN1.8 (R7), U2.27 (PB6)
/PB7: J4.17, RN1.9 (R8), U2.28 (PB7)
/PC0: J4.4, RN2.2 (R1), U2.16 (PC0)
/PC1: J4.6, RN2.3 (R2), U2.17 (PC1)
/PC2: J4.8, RN2.4 (R3), U2.18 (PC2)
/PC3: J4.10, RN2.5 (R4), U2.19 (PC3)
/PC4: J4.12, RN2.6 (R5), U2.15 (PC4)
/PC5: J4.14, RN2.7 (R6), U2.14 (PC5)
/PC6: J4.16, RN2.8 (R7), U2.13 (PC6)
/PC7: J4.18, RN2.9 (R8), U2.11 (PC7)
/RESET: U2.39 (RESET), U8.2
/Y5: U1.13, U3.2, U3.4, U7.10 (O5)
/~#FFFF: U8.4, U12.13
/~B_IORQ: J1.13, U7.4 (E1)
/~B_M1: J1.11, U7.6 (E3)
/~B_MREQ: J1.15, U3.12
/~B_RD: J1.19, U3.1, U12.12
/~B_RFSH: J1.23, U1.4, U1.5
/~B_WR: J1.17, U3.5, U12.4
/~CS0H: U2.4 (PA1), U10.10 (I0b)
/~CS0L: U2.5 (PA0), U10.6 (I0a)
/~CS1H: U2.2 (PA3), U10.11 (I1b)
/~CS1L: U2.3 (PA2), U10.5 (I1a)
/~CS2H: U2.43 (PA5), U10.12 (I2b)
/~CS2L: U2.44 (PA4), U10.4 (I2a)
/~CS3H: U2.41 (PA7), U10.13 (I3b)
/~CS3L: U2.42 (PA6), U10.3 (I3a)
/~PPI_RD: U2.6 (~RD), U3.3
/~PPI_WR: U2.40 (~WR), U3.6
/~RESET: J1.3, U1.9, U8.1, U11.1 (~Mr)
/~SBSLTSL30: J2.16, U4.12 (O0)
/~SBSLTSL31: J2.14, U4.11 (O1)
/~SBSLTSL32: J2.12, U4.10 (O2)
/~SBSLTSL33: J2.10, U4.9 (O3)
/~SLTSL0: J2.8, U4.4 (O0)
/~SLTSL1: J2.6, U4.5 (O1)
/~SLTSL2: J2.4, U4.6 (O2)
/~SLTSL3: J2.2, U4.7 (O3), U4.15 (E), U12.2, U12.10
/~SSCS0H: U11.5 (Q1), U13.10 (I0b), U14.4 (I1a)
/~SSCS0L: U11.2 (Q0), U13.6 (I0a), U14.2 (I0a)
/~SSCS1H: U11.9 (Q3), U13.11 (I1b), U14.8 (I3a)
/~SSCS1L: U11.6 (Q2), U13.5 (I1a), U14.6 (I2a)
/~SSCS2H: U11.15 (Q5), U13.12 (I2b), U14.13 (I1b)
/~SSCS2L: U11.12 (Q4), U13.4 (I2a), U14.11 (I0b)
/~SSCS3H: U11.19 (Q7), U13.13 (I3b), U14.17 (I3b)
/~SSCS3L: U11.16 (Q6), U13.3 (I3a), U14.15 (I2b)
unnamed: D1.2 (A), R1.2
unnamed: U1.3, U3.10
unnamed: U1.6, U3.13
unnamed: U1.10, U1.11
unnamed: U3.11, U4.1 (E)
unnamed: U5.6, U9.1
unnamed: U5.8, U9.2
unnamed: U6.6, U9.4
unnamed: U6.8, U9.5
unnamed: U3.8, U7.5 (E2)
unnamed: U1.8, U1.12, U10.1 (Ea), U10.15 (Eb)
unnamed: U4.2 (A0), U10.7 (Za)
unnamed: U4.3 (A1), U10.9 (Zb)
unnamed: U8.6, U11.11 (Cp)
unnamed: U8.5, U12.6
unnamed: U8.9, U12.8
unnamed: U4.14 (A0), U13.7 (Za)
unnamed: U4.13 (A1), U13.9 (Zb)
unnamed: U8.8, U14.1 (OEa), U14.19 (OEb)
