damouze/SZC-1/boards/extra/mmu_board/mmu_board.kicad_pcb

## KiCad design boards/extra/mmu_board/mmu_board.kicad_pcb (2023-10-09)

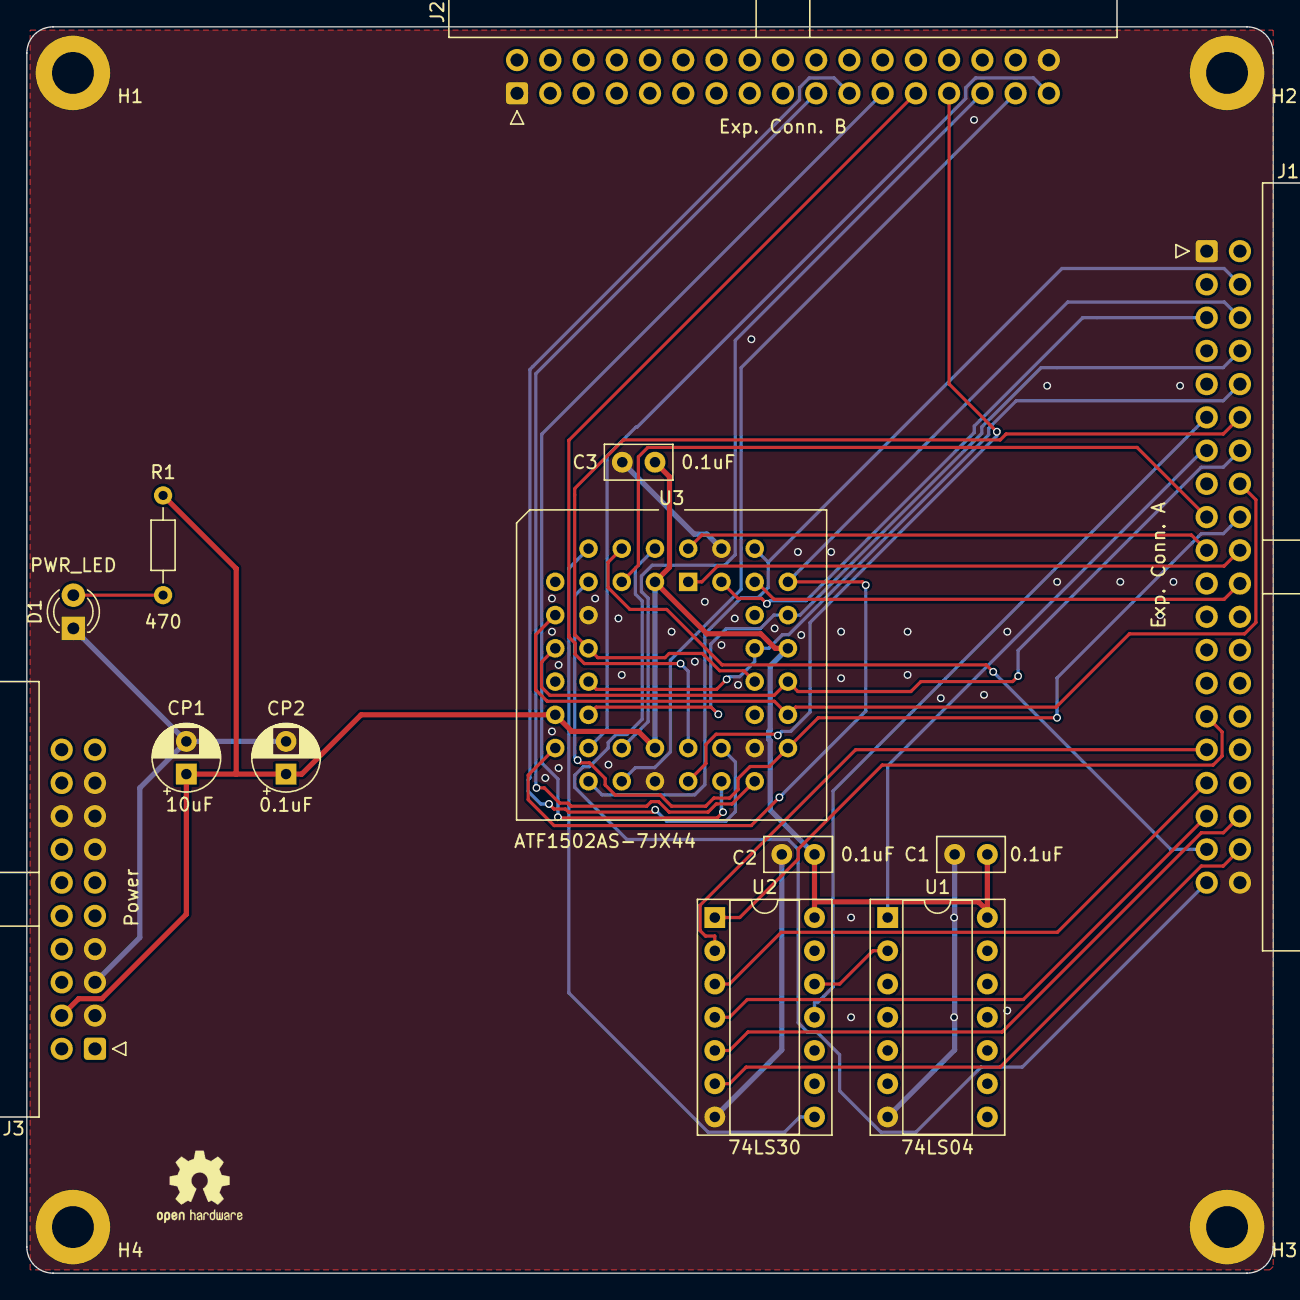
[picture p123: board mmu_board.kicad_pcb from above]

Board: 2 copper layers, 95.2 x 95.2 mm, 17 parts (0 on the bottom side), 36 nets.

Parts:
C1, C2, C3: 0.1uF; C_Disc_D5.0mm_W2.5mm_P2.50mm
CP1: 10uF; CP_Radial_D5.0mm_P2.50mm
CP2: 0.1uF; CP_Radial_D5.0mm_P2.50mm
D1: PWR_LED; LED_D3.0mm
H1, H2, H3, H4: MountingHole_Pad; MountingHole_3.2mm_M3_ISO7380_Pad
J1: Exp. Conn. A; IDC-Header_2x20_P2.54mm_Horizontal
J2: Exp. Conn. B; IDC-Header_2x17_P2.54mm_Horizontal
J3: Power; IDC-Header_2x10_P2.54mm_Horizontal
R1: 470; R_Axial_DIN0204_L3.6mm_D1.6mm_P7.62mm_Horizontal
U1: 74LS04; DIP-14_W7.62mm_Socket
U2: 74LS30; DIP-14_W7.62mm_Socket
U3: ATF1502AS-7JX44; PLCC-44_THT-Socket

Connections:
/+5V: C1.1, C2.1, C3.1, CP1.1, CP2.1, J3.4, R1.1, U1.14 (VCC), U2.14 (VCC), U3.3 (VCC), U3.15 (VCC), U3.23 (VCC), U3.35 (VCC)
/BUS_CLK: J1.5, U3.43 (GCLK1/I)
/B_A0: J1.39, U3.2 (GCLK2/OE2/I)
/B_A1: J1.37, U3.4 (I/O)
/B_A2: J1.35, U2.4
/B_A3: J1.33, U2.3
/B_A4: J1.31, U2.2
/B_A5: J1.29, U2.1
/B_A6: J1.38, U2.6
/B_A7: J1.36, U2.5
/B_A14: J1.22, U3.41 (GCLK3/I/O)
/B_A15: J1.20, U3.1 (GCLR/I)
/B_D0: J1.18, U3.8 (I/O), U3.29 (I/O)
/B_D1: J1.16, U3.9 (I/O), U3.31 (I/O)
/B_D2: J1.14, U3.11 (PD1/I/O), U3.33 (I/O)
/B_D3: J1.12, U3.12 (I/O), U3.34 (I/O)
/B_D4: J1.10, U3.14 (I/O), U3.36 (I/O)
/B_D5: J1.8, U3.16 (I/O), U3.37 (I/O)
/B_D6: J1.6, U3.17 (I/O), U3.39 (I/O)
/B_D7: J1.4, U3.18 (I/O), U3.40 (I/O)
/GND: C1.2, C2.2, C3.2, CP1.2, CP2.2, D1.1 (K), H1.1, H2.1, H3.1, H4.1, J1.1, J1.40, J2.1, J2.34, J3.3, J3.5, J3.7, J3.13, J3.15, J3.16, J3.17, U1.7 (GND), U2.7 (GND), U3.10 (GND), U3.22 (GND), U3.30 (GND), U3.42 (GND)
/IORQ: U1.2, U2.12
/M_A14: J2.33, U3.19 (I/O)
/M_A15: J2.31, U3.20 (I/O)
/M_A16: J2.29, U3.21 (I/O)
/M_A17: J2.27, U3.24 (I/O)
/M_A18: J2.25, U3.25 (PD2/I/O)
/M_A19: J2.23, U3.26 (I/O)
/M_A20: J2.21, U3.27 (I/O)
/M_A21: J2.19, U3.28 (I/O)
/~B_IORQ: J1.13, U1.1
/~B_M1: J1.11, U2.11
/~B_RD: J1.19, U3.44 (OE1/I)
/~B_WR: J1.17, U3.5 (I/O)
/~MMU_CS: U2.8, U3.6 (I/O)
unnamed: D1.2 (A), R1.2
