damouze/SZC-1/boards/msx_compat/msx_rom_board/msx_rom_board.kicad_pcb

## KiCad design boards/msx_compat/msx_rom_board/msx_rom_board.kicad_pcb (2023-10-09)

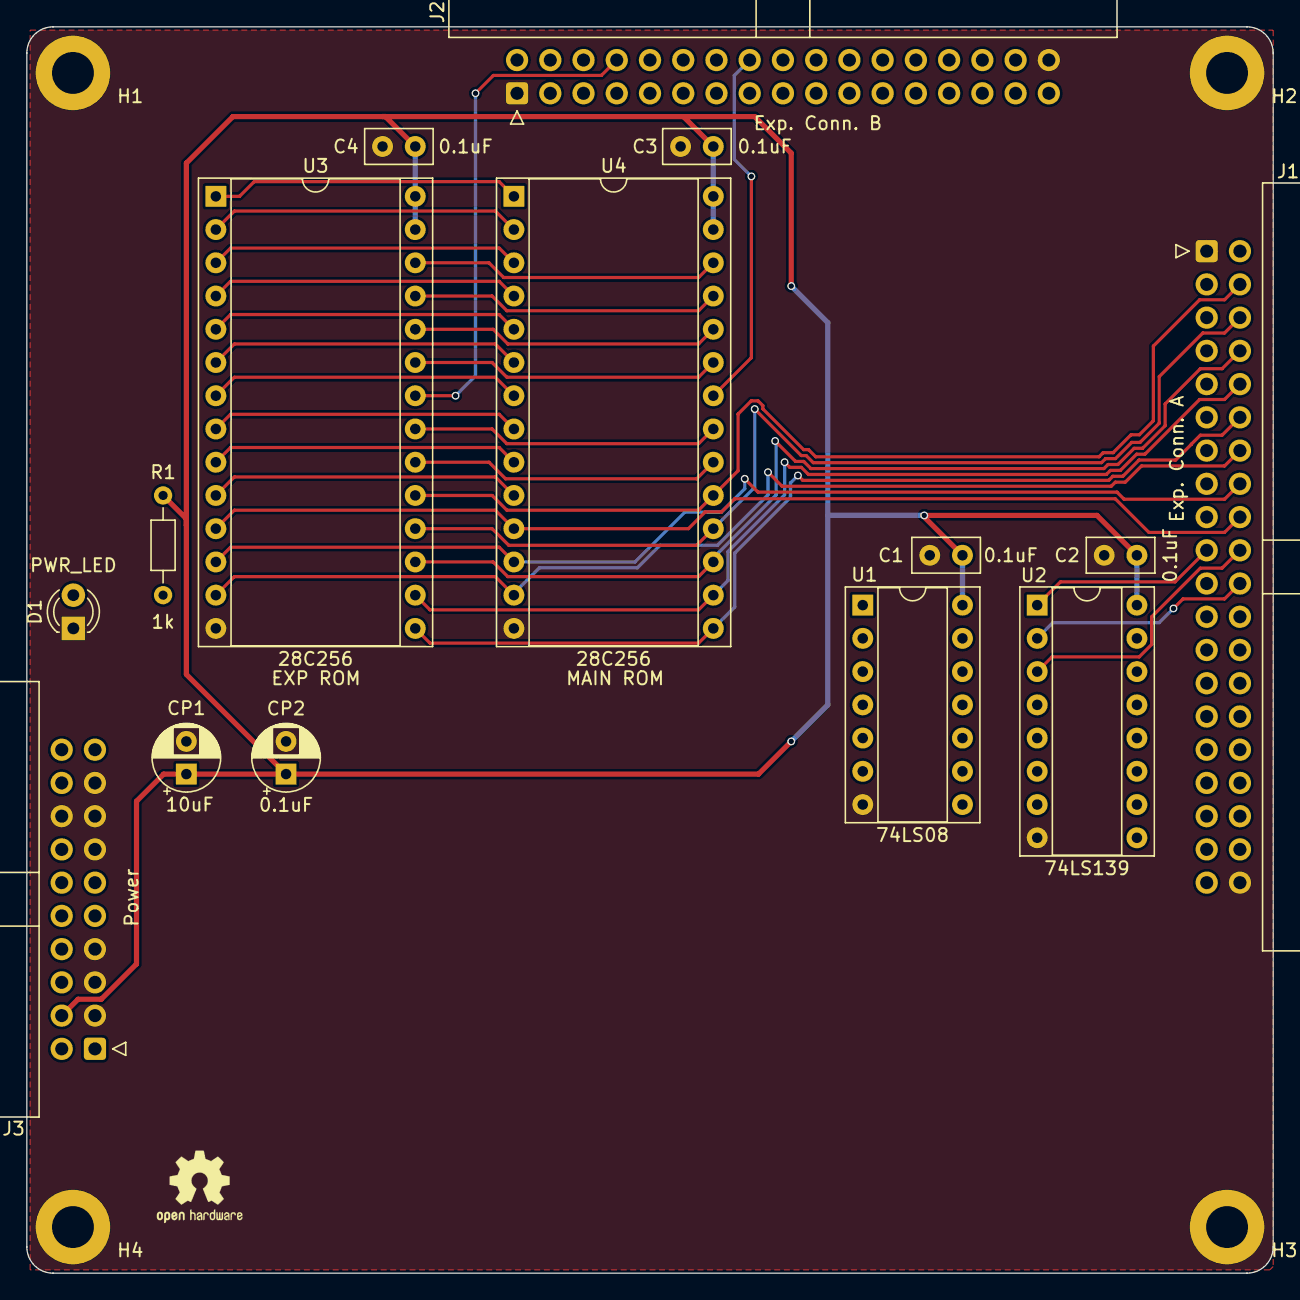
[picture p124: board msx_rom_board.kicad_pcb from above]

Board: 2 copper layers, 95.2 x 95.2 mm, 19 parts (0 on the bottom side), 33 nets.

Parts:
C1, C2, C3, C4: 0.1uF; C_Disc_D5.0mm_W2.5mm_P2.50mm
CP1: 10uF; CP_Radial_D5.0mm_P2.50mm
CP2: 0.1uF; CP_Radial_D5.0mm_P2.50mm
D1: PWR_LED; LED_D3.0mm
H1, H2, H3, H4: MountingHole_Pad; MountingHole_3.2mm_M3_ISO7380_Pad
J1: Exp. Conn. A; IDC-Header_2x20_P2.54mm_Horizontal
J2: Exp. Conn. B; IDC-Header_2x17_P2.54mm_Horizontal
J3: Power; IDC-Header_2x10_P2.54mm_Horizontal
R1: 1k; R_Axial_DIN0204_L3.6mm_D1.6mm_P7.62mm_Horizontal
U1: 74LS08; DIP-14_W7.62mm_Socket
U2: 74LS139; DIP-16_W7.62mm_Socket
U3, U4: 28C256; DIP-28_W15.24mm_Socket

Connections:
/+5V: C1.1, C2.1, C3.1, C4.1, CP1.1, CP2.1, J3.4, R1.1, U1.14 (VCC), U2.16 (VCC), U3.27 (~WE), U3.28 (VCC), U4.27 (~WE), U4.28 (VCC)
/B_A0: J1.39, U3.10 (A0), U4.10 (A0)
/B_A1: J1.37, U3.9 (A1), U4.9 (A1)
/B_A2: J1.35, U3.8 (A2), U4.8 (A2)
/B_A3: J1.33, U3.7 (A3), U4.7 (A3)
/B_A4: J1.31, U3.6 (A4), U4.6 (A4)
/B_A5: J1.29, U3.5 (A5), U4.5 (A5)
/B_A6: J1.38, U3.4 (A6), U4.4 (A6)
/B_A7: J1.36, U3.3 (A7), U4.3 (A7)
/B_A8: J1.34, U3.25 (A8), U4.25 (A8)
/B_A9: J1.32, U3.24 (A9), U4.24 (A9)
/B_A10: J1.30, U3.21 (A10), U4.21 (A10)
/B_A11: J1.28, U3.23 (A11), U4.23 (A11)
/B_A12: J1.26, U3.2 (A12), U4.2 (A12)
/B_A13: J1.24, U3.26 (A13), U4.26 (A13)
/B_A14: J1.22, U2.2 (A0), U3.1 (A14), U4.1 (A14)
/B_A15: J1.20, U2.3 (A1)
/B_D0: J1.18, U3.11 (D0), U4.11 (D0)
/B_D1: J1.16, U3.12 (D1), U4.12 (D1)
/B_D2: J1.14, U3.13 (D2), U4.13 (D2)
/B_D3: J1.12, U3.15 (D3), U4.15 (D3)
/B_D4: J1.10, U3.16 (D4), U4.16 (D4)
/B_D5: J1.8, U3.17 (D5), U4.17 (D5)
/B_D6: J1.6, U3.18 (D6), U4.18 (D6)
/B_D7: J1.4, U3.19 (D7), U4.19 (D7)
/GND: C1.2, C2.2, C3.2, C4.2, CP1.2, CP2.2, D1.1 (K), H1.1, H2.1, H3.1, H4.1, J1.1, J1.40, J2.1, J2.34, J3.3, J3.5, J3.7, J3.13, J3.15, J3.16, J3.17, U1.7 (GND), U2.8 (GND), U3.14 (GND), U4.14 (GND)
/~B_RD: J1.19, U2.1 (E)
/~ROMHI_CS: U1.5, U2.5 (O1)
/~ROMLO_CS: U1.4, U2.4 (O0)
/~ROM_CS: U1.6, U3.20 (~CS), U4.20 (~CS)
/~SBSLTSL30: J2.16, U4.22 (~OE)
/~SLTSL0: J2.8, U3.22 (~OE)
unnamed: D1.2 (A), R1.2
